MakerWear/MakerWear/Common/Wiki/images/Action/LightBar.png

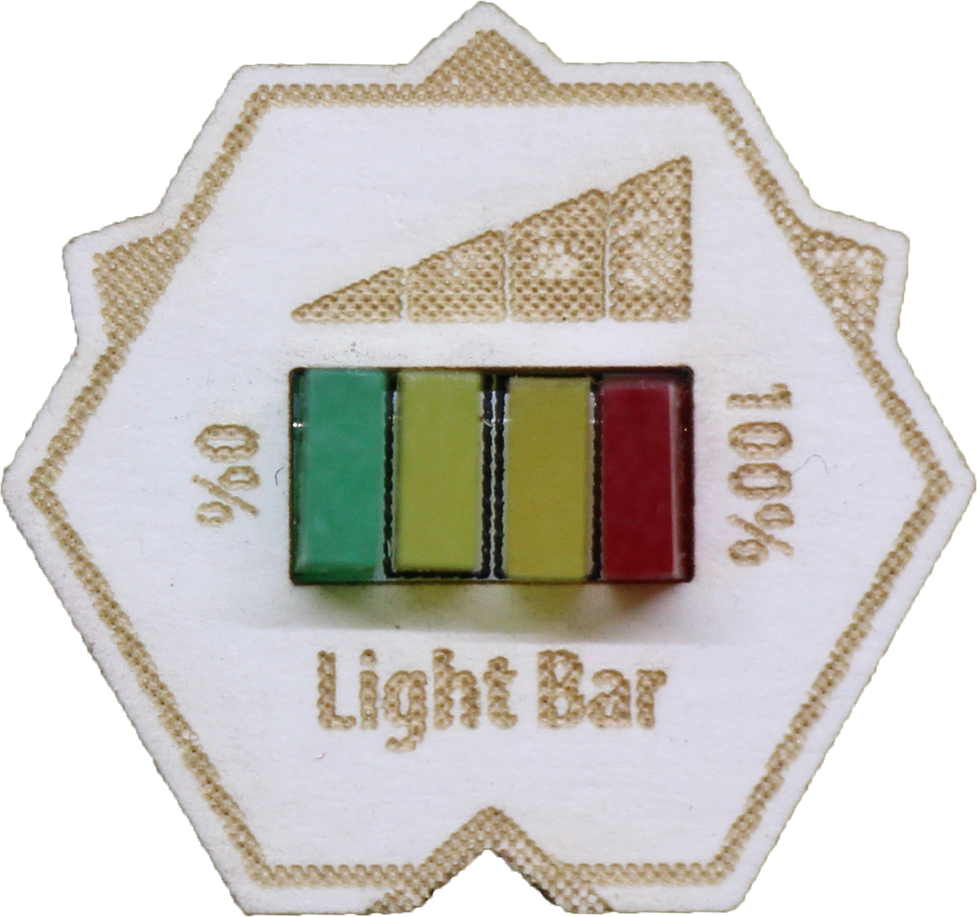
Common/Wiki/images/Action/LightBar.png
