MakerWear/MakerWear/Common/Wiki/images/Action/MultiColorLight.png

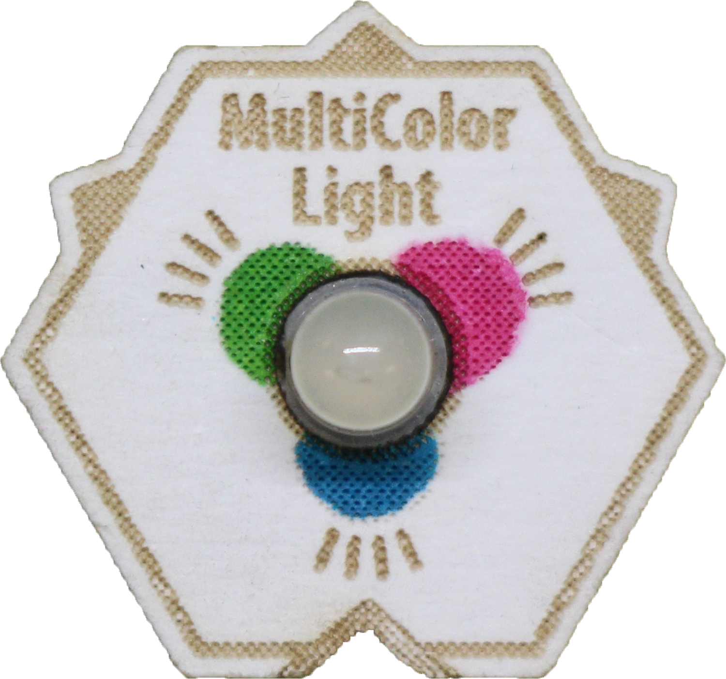
Common/Wiki/images/Action/MultiColorLight.png
