MakerWear/MakerWear/Common/Wiki/images/Action/Number.png

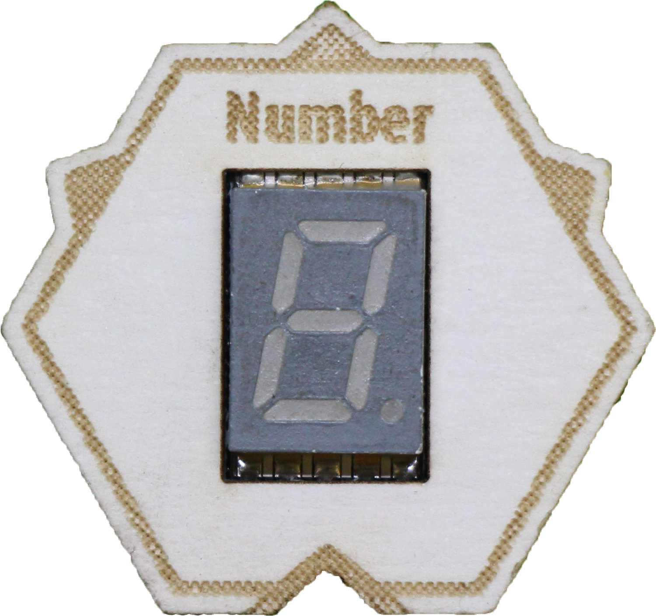
Common/Wiki/images/Action/Number.png
