MakerWear/MakerWear/Common/Wiki/images/Action/RotatorWithPropeller.png

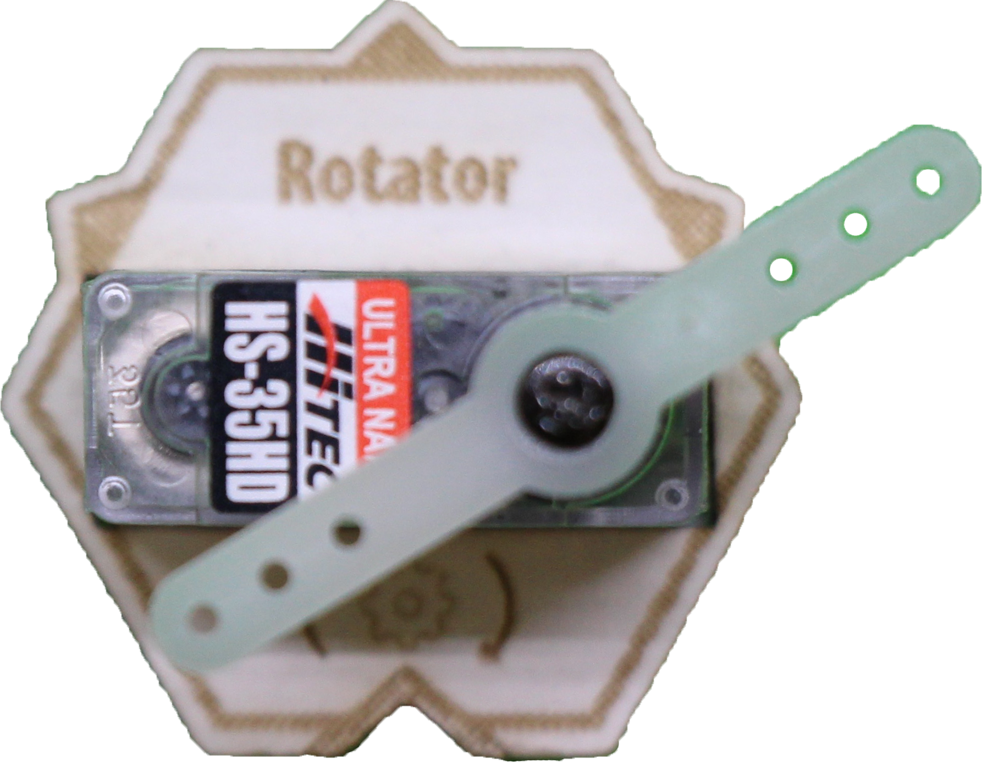
Common/Wiki/images/Action/RotatorWithPropeller.png
