MakerWear/MakerWear/Common/Wiki/images/Action/Sender.png

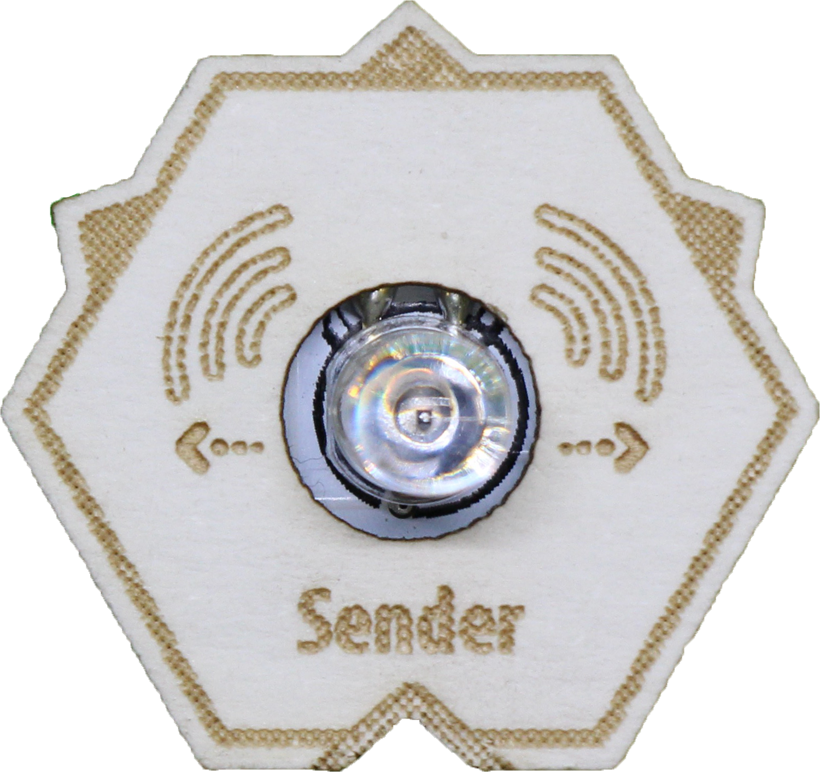
Common/Wiki/images/Action/Sender.png
