MakerWear/MakerWear/Common/Wiki/images/Action/SingleLightRed.png

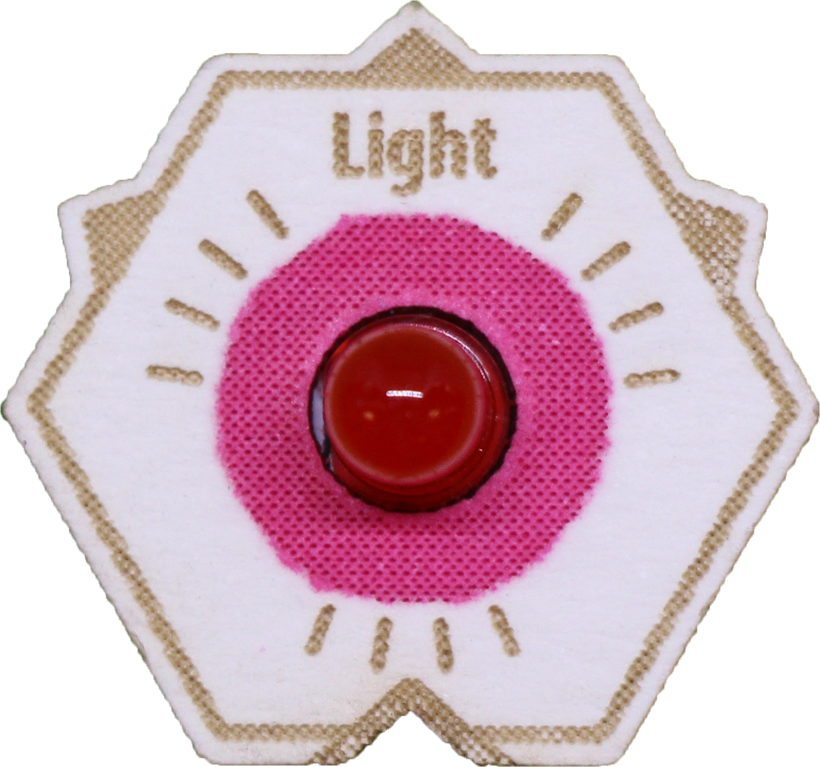
Common/Wiki/images/Action/SingleLightRed.png
