MakerWear/MakerWear/Common/Wiki/images/Action/Spinner_v2.png

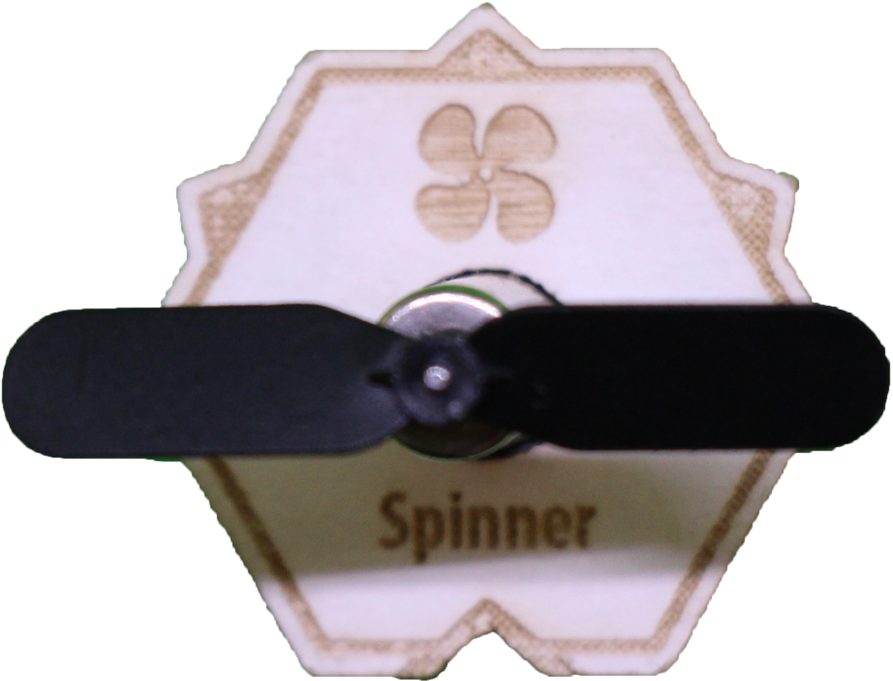
Common/Wiki/images/Action/Spinner_v2.png
