MakerWear/MakerWear/Common/Wiki/images/Action/Vibration.png

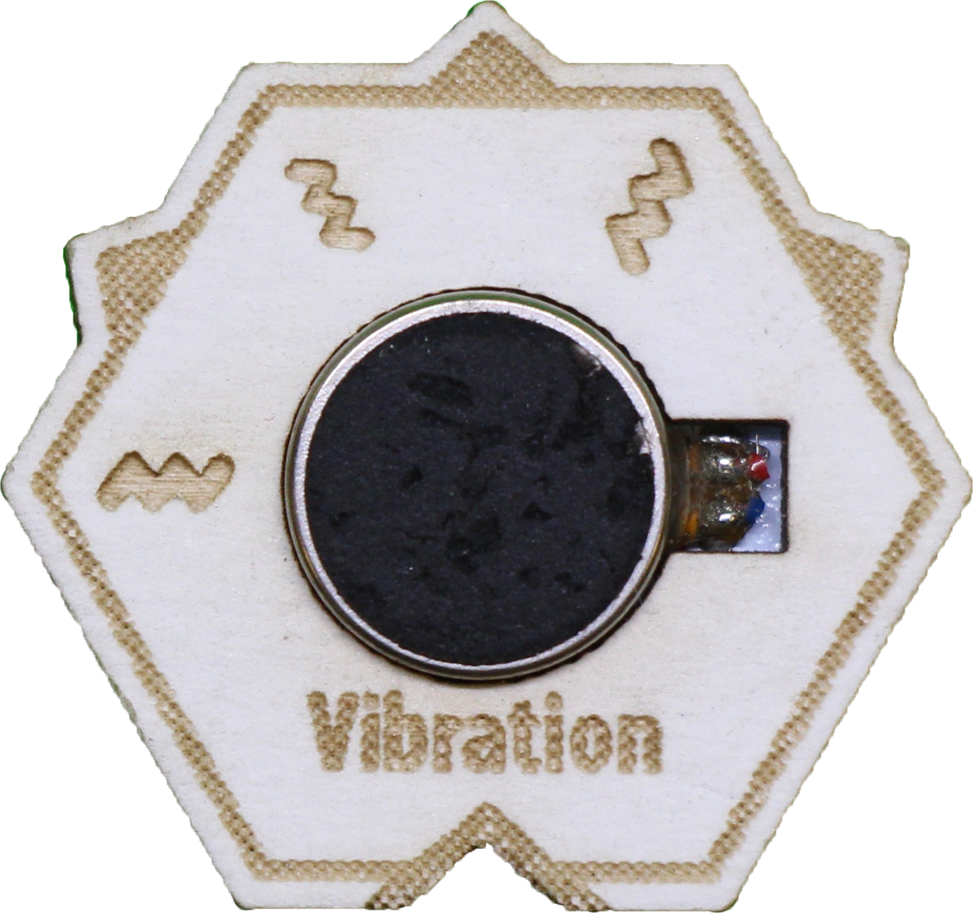
Common/Wiki/images/Action/Vibration.png
