MakerWear/MakerWear/Common/Wiki/images/header.JPG

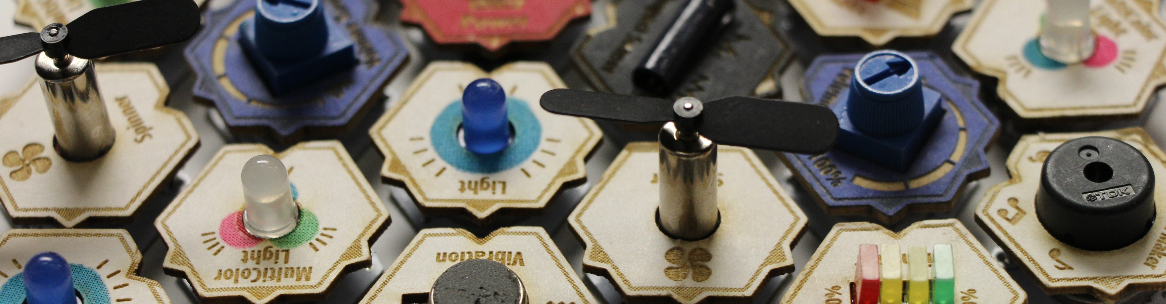
Common/Wiki/images/header.JPG
