MakerWear/MakerWear/Common/Wiki/images/Misc/DIY.png

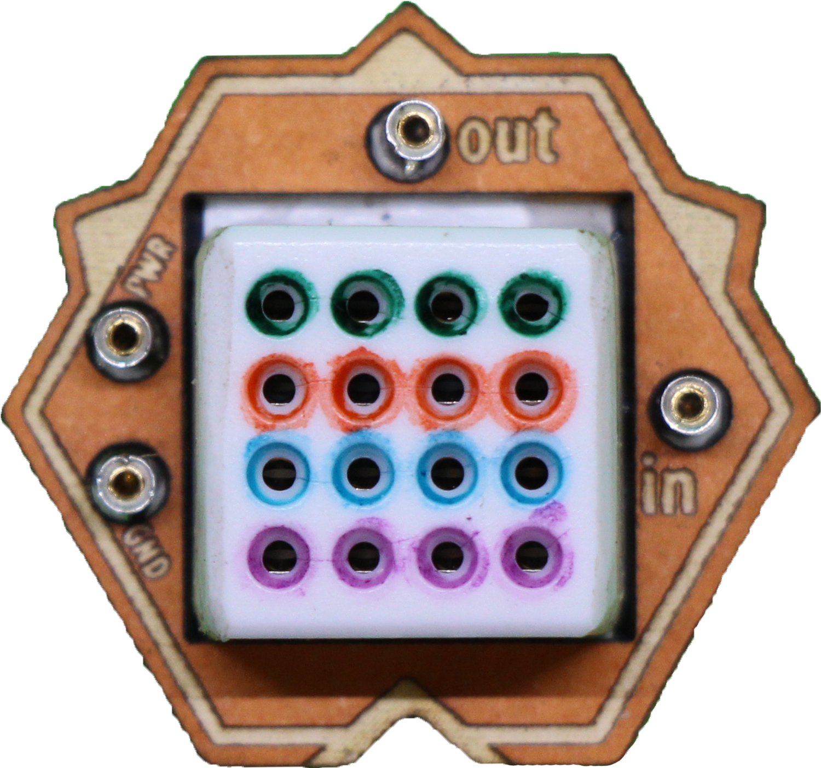
Common/Wiki/images/Misc/DIY.png
