MakerWear/MakerWear/Common/Wiki/images/Misc/Dummy.png

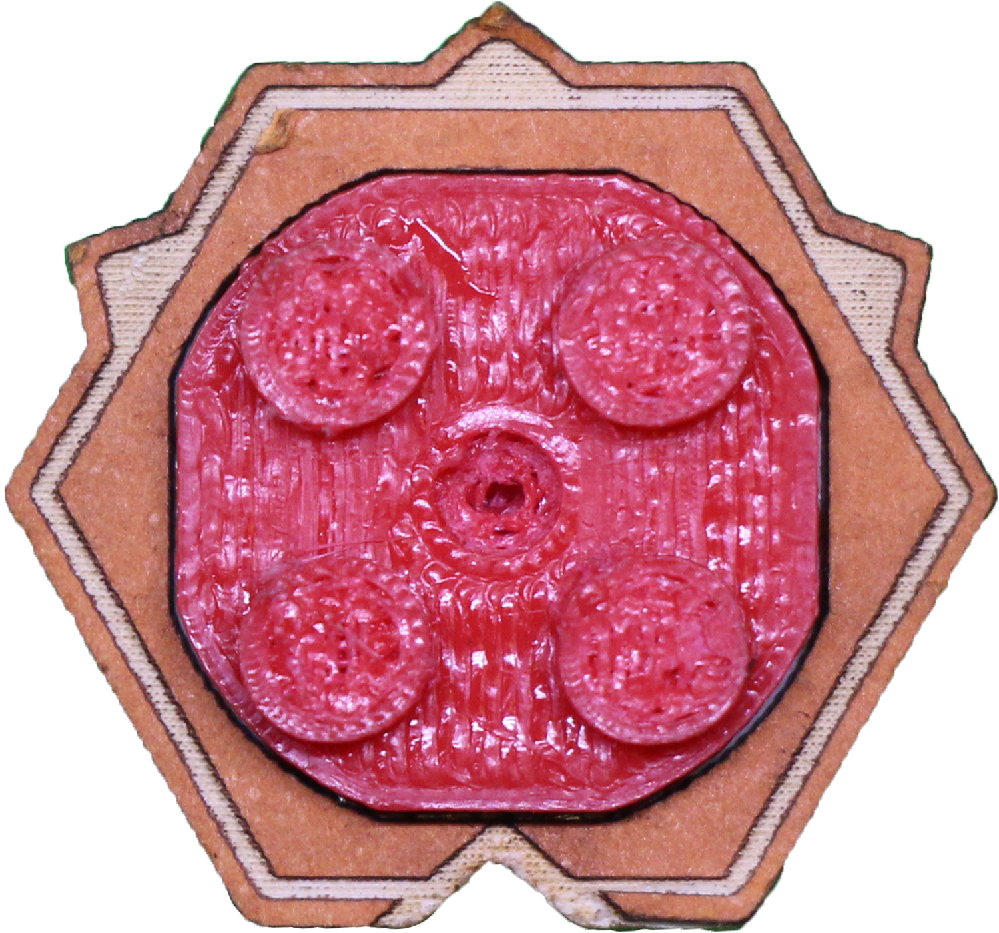
Common/Wiki/images/Misc/Dummy.png
