MakerWear/MakerWear/Common/Wiki/images/Misc/WireEnd.png

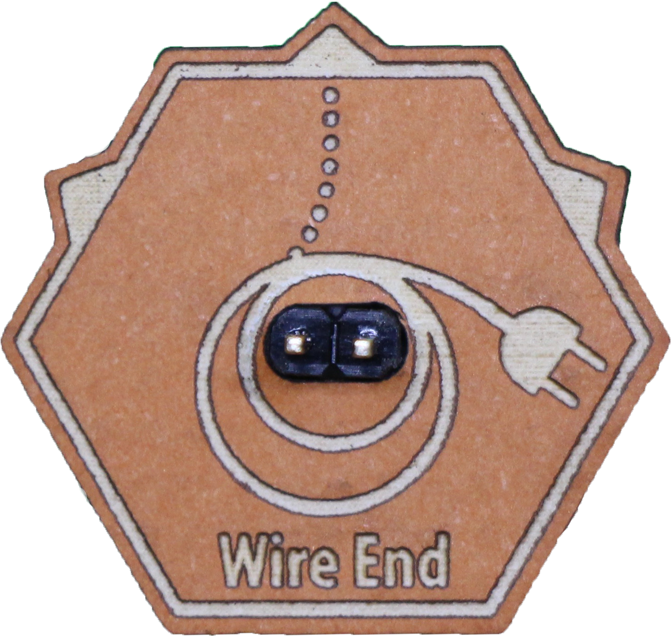
Common/Wiki/images/Misc/WireEnd.png
