MakerWear/MakerWear/Common/Wiki/images/Misc/WireStart.png

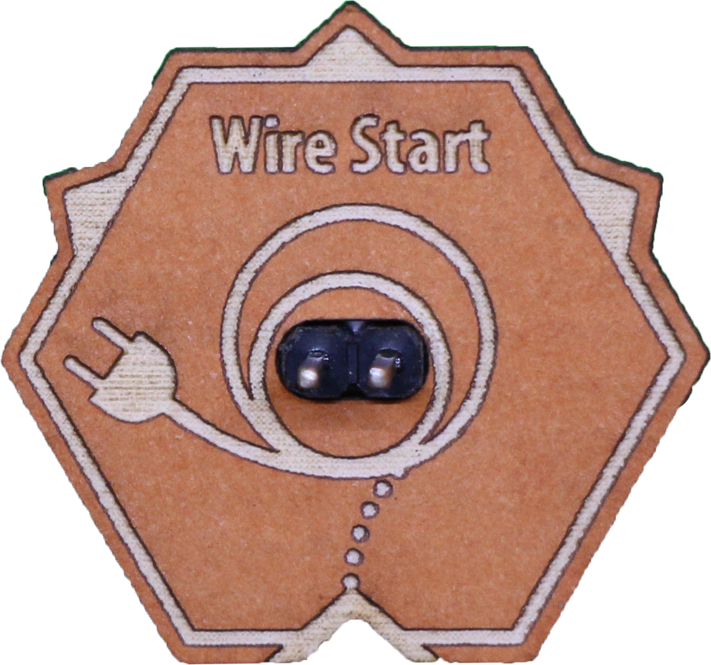
Common/Wiki/images/Misc/WireStart.png
