MakerWear/MakerWear/Common/Wiki/images/Modifier/Counter.png

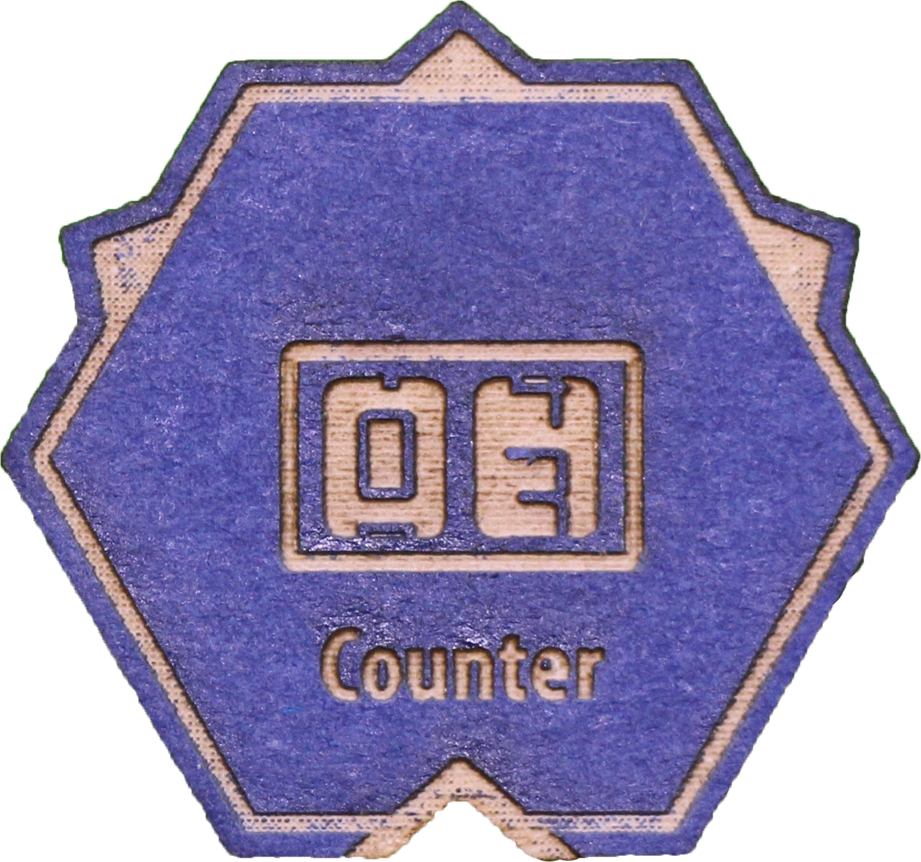
Common/Wiki/images/Modifier/Counter.png
