MakerWear/MakerWear/Common/Wiki/images/Modifier/Fade.png

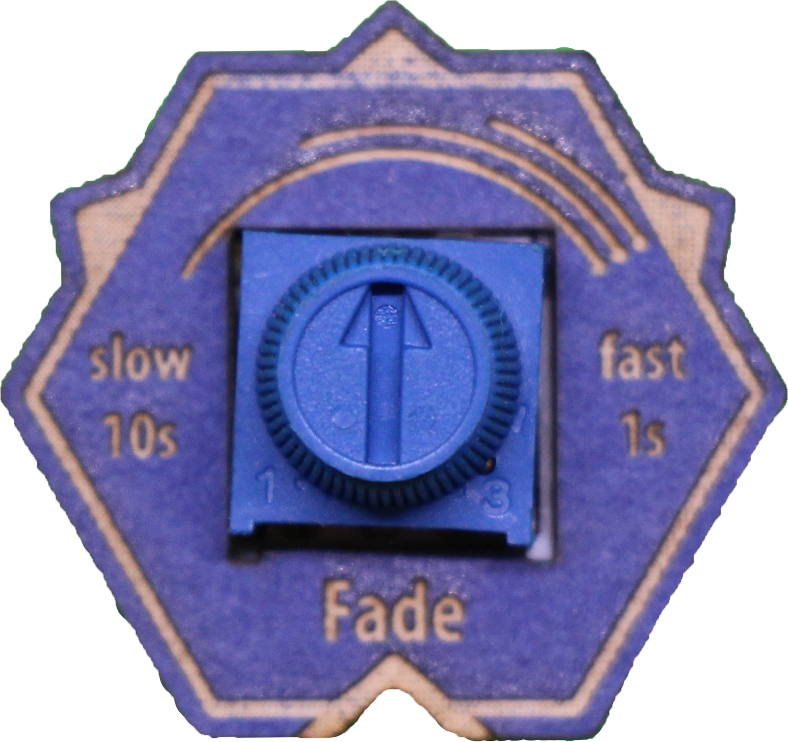
Common/Wiki/images/Modifier/Fade.png
