MakerWear/MakerWear/Common/Wiki/images/Modifier/Inverter.png

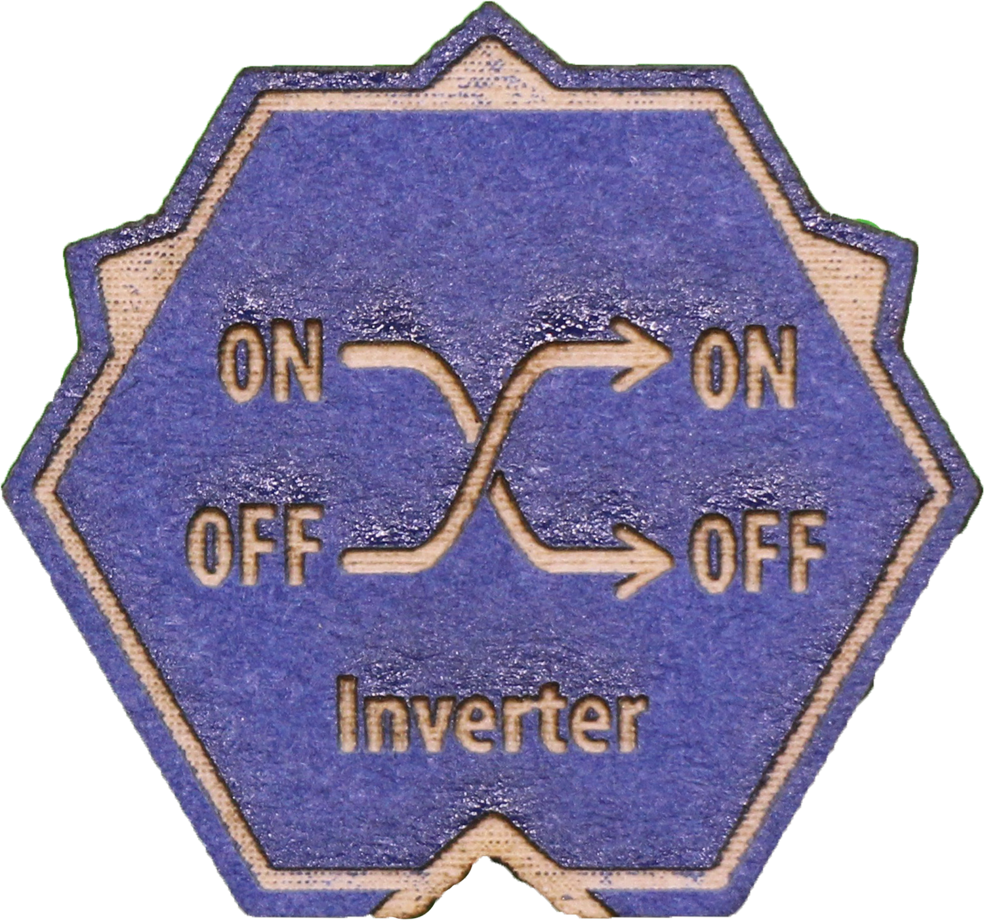
Common/Wiki/images/Modifier/Inverter.png
