MakerWear/MakerWear/Common/Wiki/images/Modifier/SineWave.png

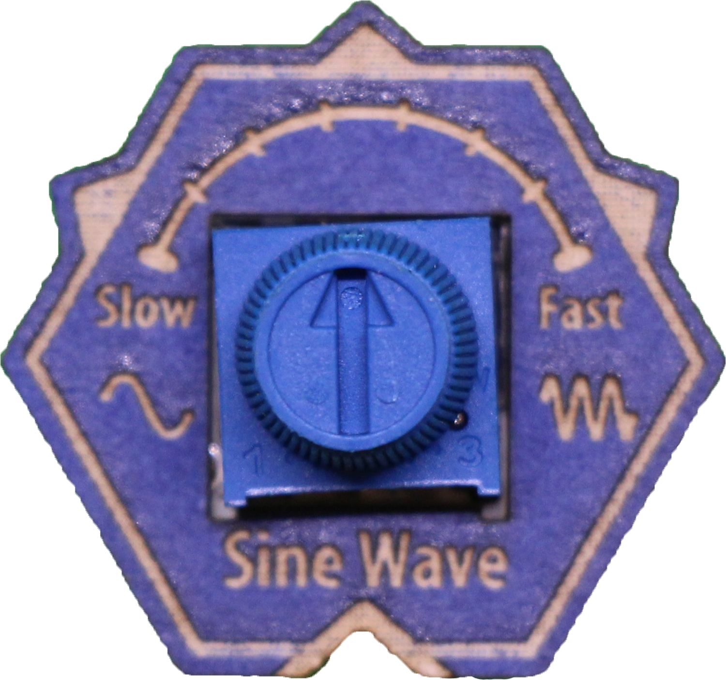
Common/Wiki/images/Modifier/SineWave.png
