MakerWear/MakerWear/Common/Wiki/images/Modifier/SquareWave.png

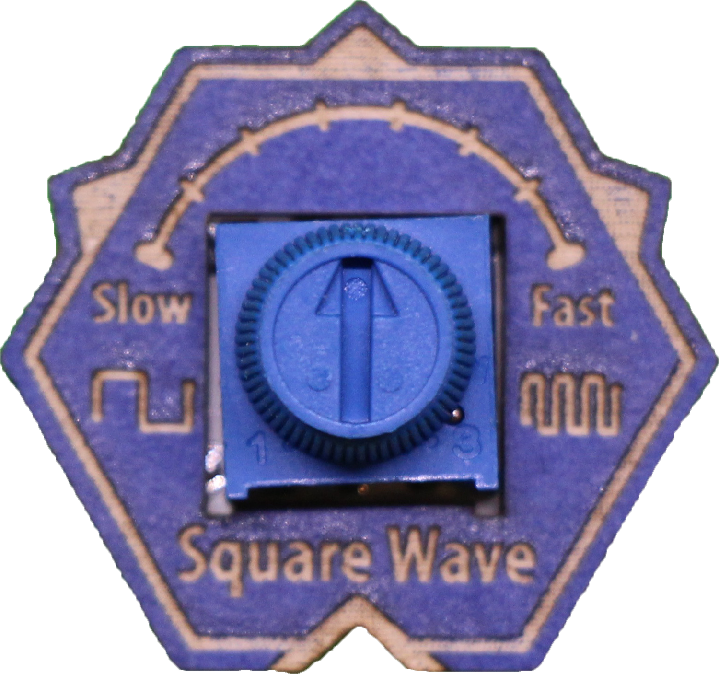
Common/Wiki/images/Modifier/SquareWave.png
