MakerWear/MakerWear/Common/Wiki/images/Modifier/VolumeKnob.png

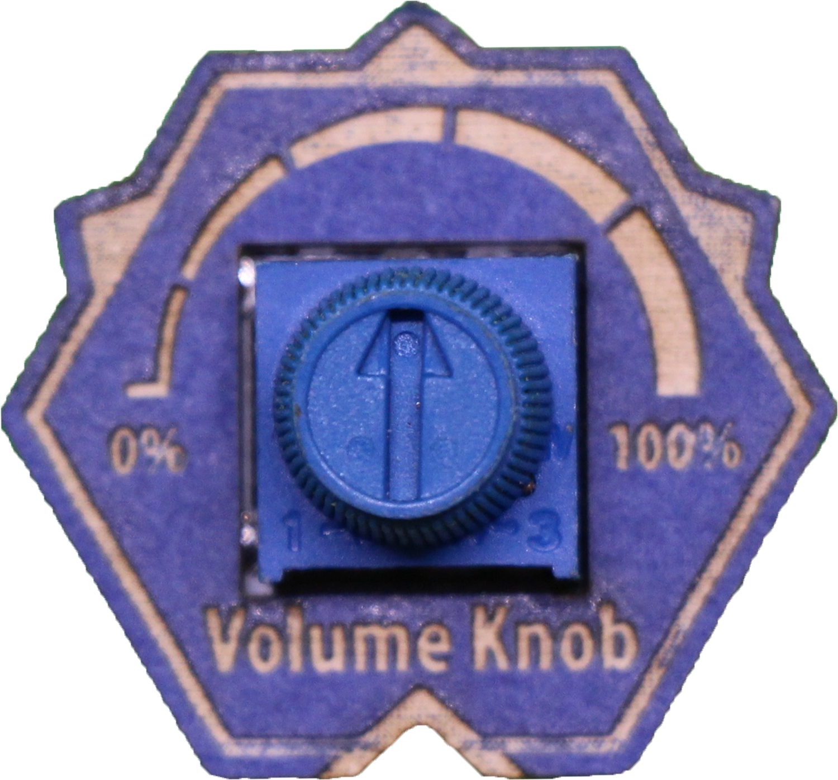
Common/Wiki/images/Modifier/VolumeKnob.png
