MakerWear/MakerWear/Common/Wiki/images/Power/power.png

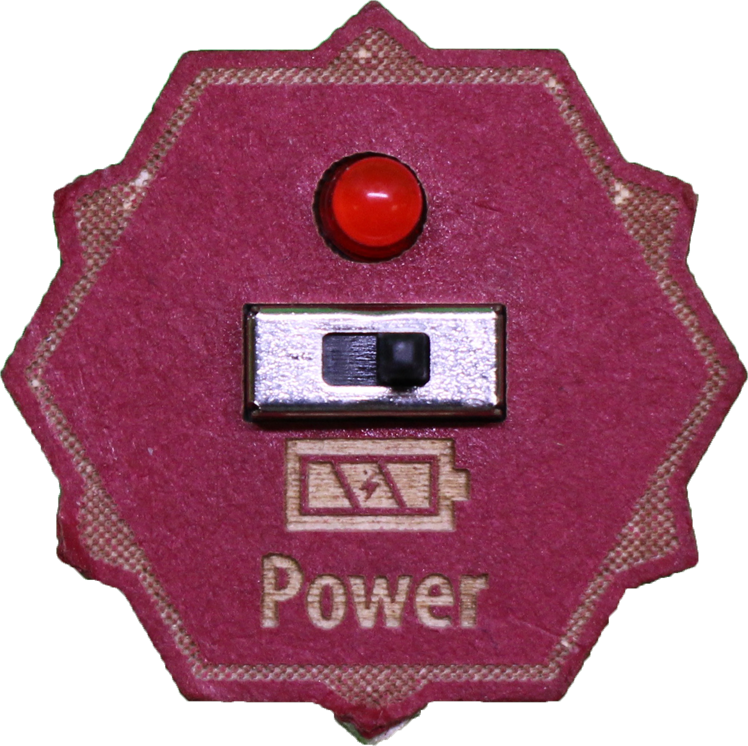
Common/Wiki/images/Power/power.png
