MakerWear/MakerWear/Common/Wiki/images/Sensor/ColorDetector.png

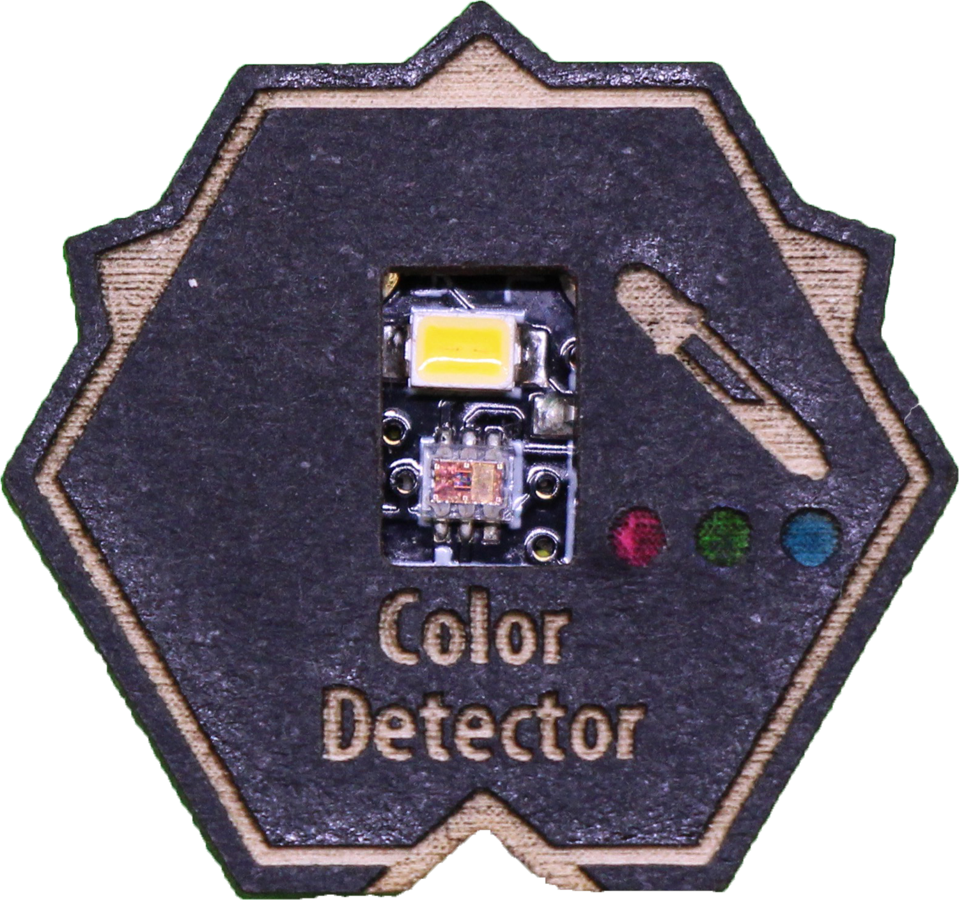
Common/Wiki/images/Sensor/ColorDetector.png
