MakerWear/MakerWear/Common/Wiki/images/Sensor/DistanceSensor.png

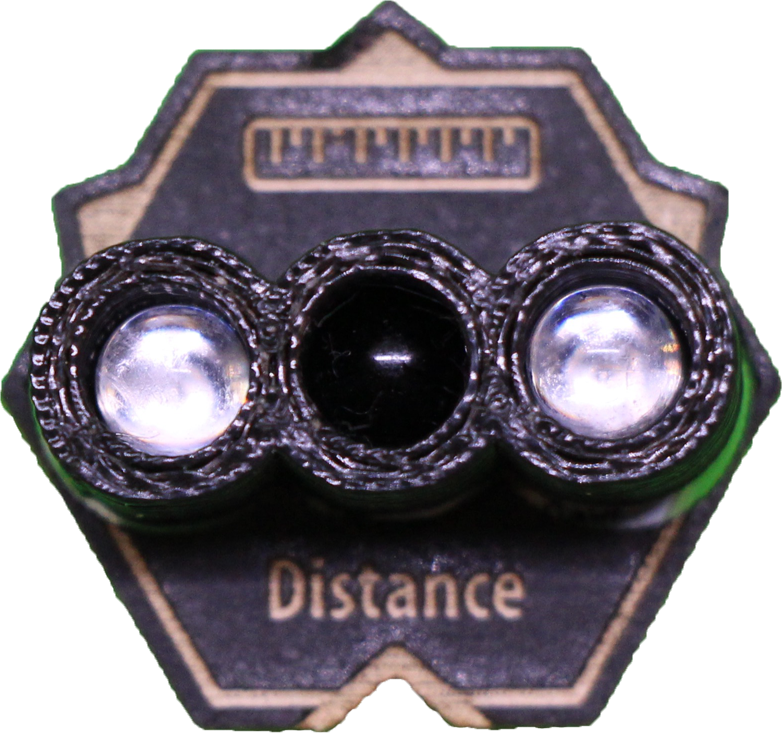
Common/Wiki/images/Sensor/DistanceSensor.png
