MakerWear/MakerWear/Common/Wiki/images/Sensor/ImpactSensor.png

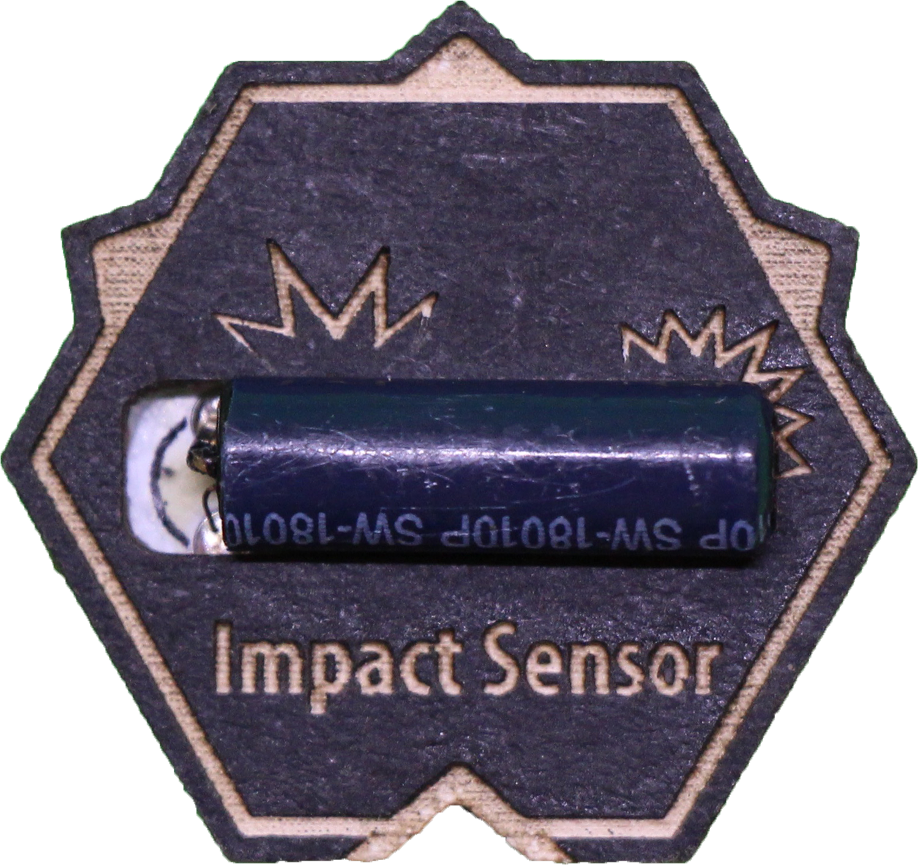
Common/Wiki/images/Sensor/ImpactSensor.png
