MakerWear/MakerWear/Common/Wiki/images/Sensor/MotionDetector.png

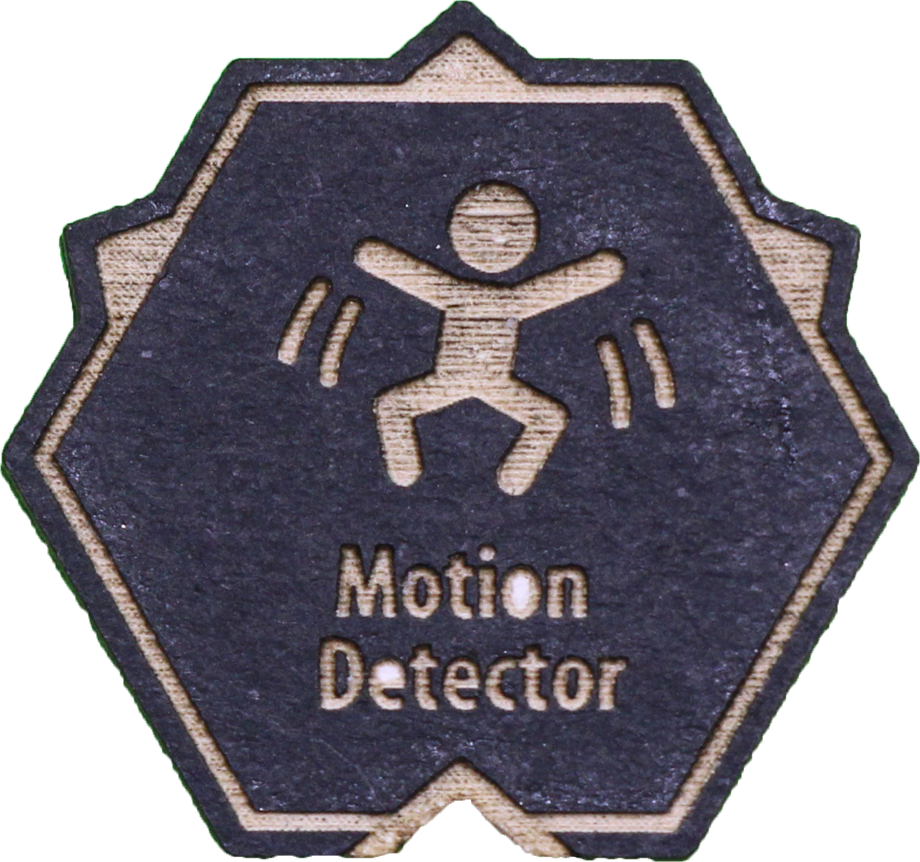
Common/Wiki/images/Sensor/MotionDetector.png
