MakerWear/MakerWear/Common/Wiki/images/Sensor/Receiver.png

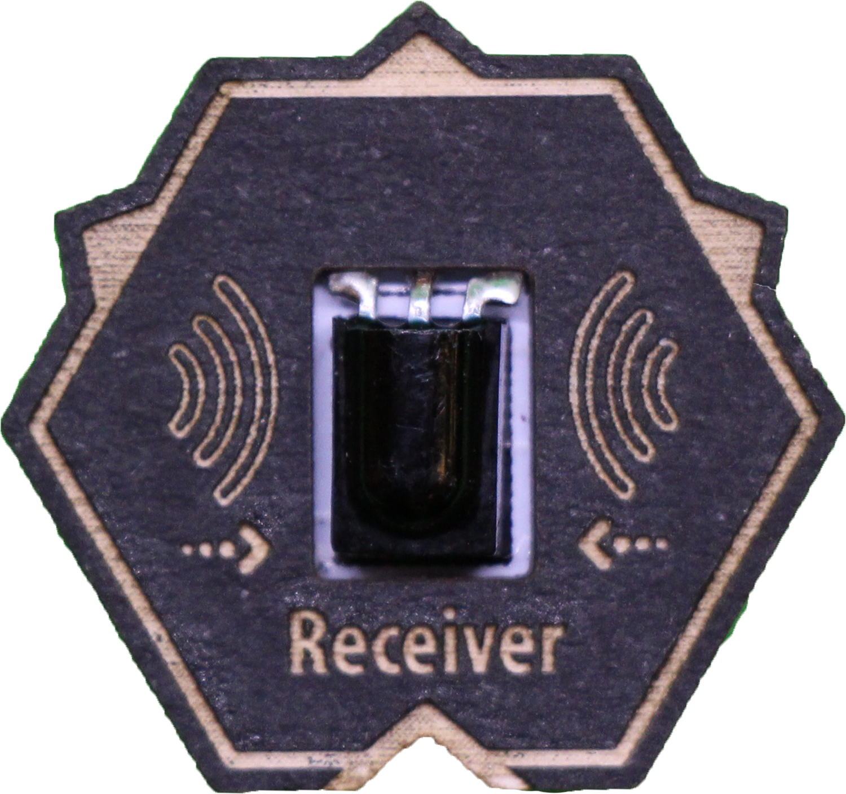
Common/Wiki/images/Sensor/Receiver.png
