MakerWear/MakerWear/Common/Wiki/images/Sensor/TemperatureSensor.png

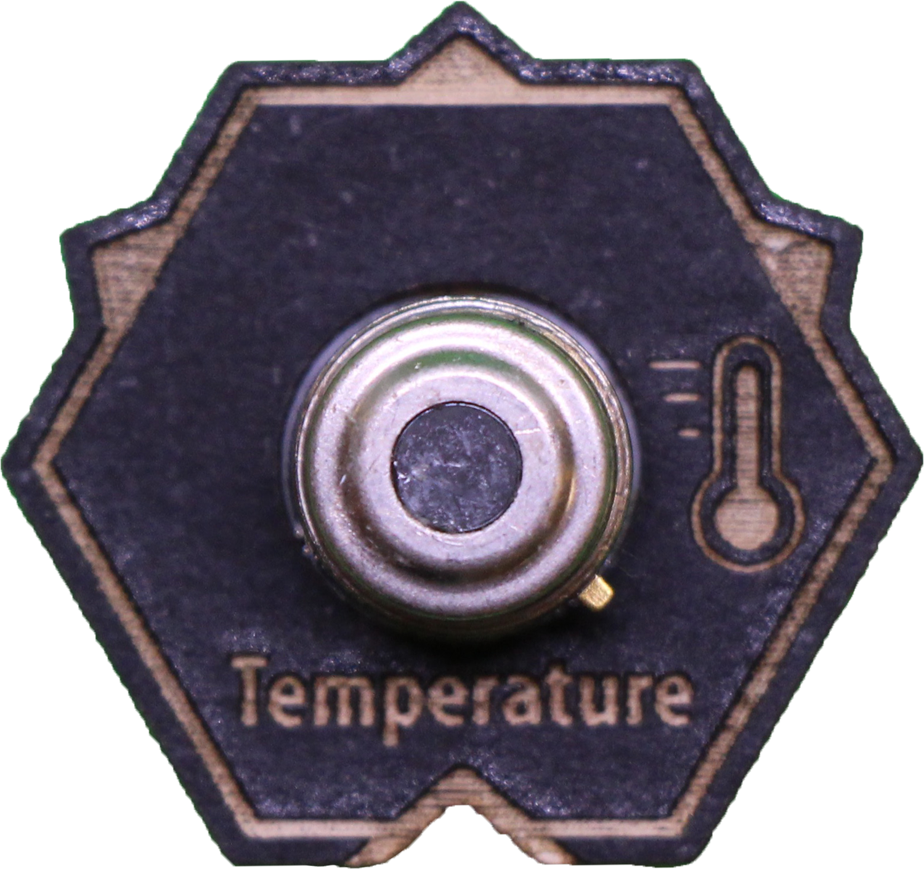
Common/Wiki/images/Sensor/TemperatureSensor.png
