MakerWear/MakerWear/Common/Wiki/images/Sensor/TiltSensor.png

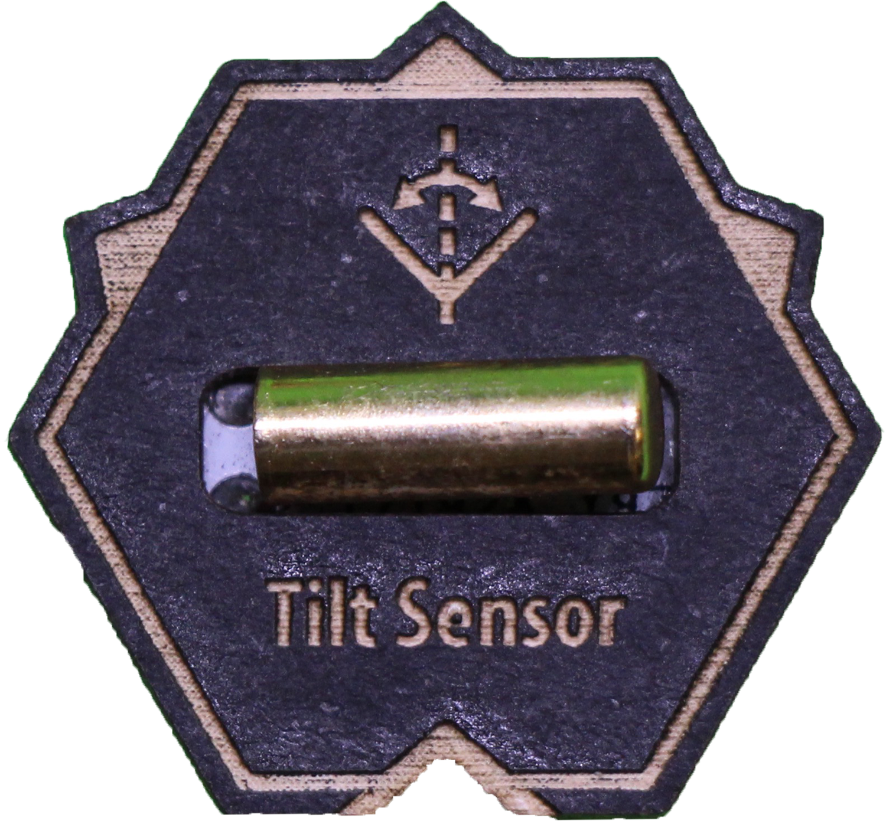
Common/Wiki/images/Sensor/TiltSensor.png
