MakerWear/MakerWear/Modules/Sensor/DistanceSensor/ArduinoCodes/2LEDcurve.jpg

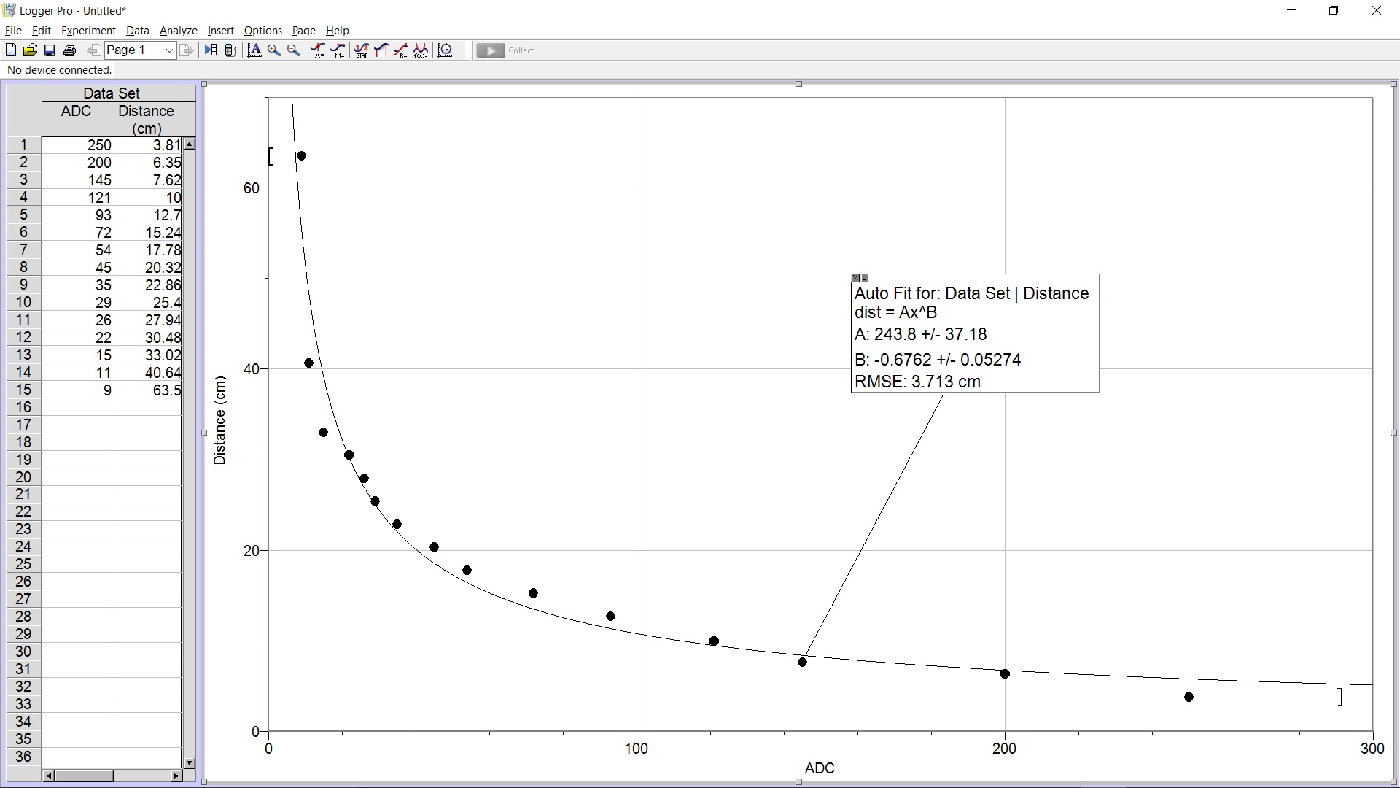
Modules/Sensor/DistanceSensor/ArduinoCodes/2LEDcurve.jpg
