MakerWear/MakerWear/Modules/Misc/ProgrammableOLED/EagleDesigns/ComponentList.xlsx

Name | Link | Dimensions | Count | Price | Notes
Micro OLED | https://www.sparkfun.com/products/13003 |  | 1 |  | For making this module, we desoldered the OLED from the Sparkfun breakout board using a soldering Iron and soldered it on top of our own custom PCB
ATmega328P-AU-ND | http://www.digikey.com/short/3pr0nz | 32TQFP | 1
Shield Finger Contact Spring | http://www.digikey.com/short/3zzmh1 | SMD | 9
1MΩ SMD Resistor | http://www.digikey.com/short/35mdtn | 0603 | 3
4x2 Pin Header | http://www.digikey.com/short/35md8j | 2.54mm Pitch | 1
4.7KΩ Resistor | http://www.digikey.com/short/35mdfh | 0603 | 3
0.22uF Capacitor | http://www.digikey.com/short/35rjqv | 0603 | 3
Micro USB Connector | http://www.digikey.com/short/35mvjp | SMD | 1
390KΩ Resistor | http://www.digikey.com/short/35rqbz | 0603
1uF Capacitor | http://www.digikey.com/short/35rq5v | 0603 | 2
