MakerWear/MakerWear/Modules/Sensor/DistanceSensor/EagleDesigns/ComponentList.xlsx

Name | Link | Dimensions | Count | Price | Notes
4.7KΩ Resistor | http://www.digikey.com/short/35mdfh | 0603 | 1
0.22uF Capacitor | http://www.digikey.com/short/35rjqv | 0603 | 1
ATtiny85-20PU | http://www.digikey.com/short/3zphbw | DIP | 1
Shield Finger Contact Spring | http://www.digikey.com/short/3zzmh1 | SMD | 6
1MΩ SMD Resistor | http://www.digikey.com/short/35mdtn | 0603 | 1
4x1 Pin Header | http://www.digikey.com/short/3zzh43 | 2.54mm Pitch | 1
Infrared Receiver | http://a.co/4VBF2Ul | Through Hole | 1
Infrared Emitter | http://a.co/4VBF2Ul | Through Hole | 2
100KΩ Resistor | https://www.digikey.com/short/3n01hw | 0603 | 1
3D Printed Casing |  |  | 1
