MakerWear/MakerWear/Modules/Sensor/LightSensor/EagleDesigns/ComponentList.xlsx

Name | Link | Dimensions | Count | Price | Notes
4.7KΩ Resistor | http://www.digikey.com/short/35mdfh | 0603 | 2
0.22uF Capacitor | http://www.digikey.com/short/35rjqv | 0603 | 1
ATtiny85-20PU | http://www.digikey.com/short/3zphbw | DIP | 1
Shield Finger Contact Spring | http://www.digikey.com/short/3zzmh1 | SMD | 6
1MΩ SMD Resistor | http://www.digikey.com/short/35mdtn | 0603 | 1
4x1 Pin Header | http://www.digikey.com/short/3zzh43 | 2.54mm Pitch | 1
330KΩ Resistor | https://www.digikey.com/short/3nvcp9 | 0603 | 1
Photoresistor | https://www.sparkfun.com/products/9088 | Through Hole | 1 |  | I was not able to find the photoresistor that we used in our current modules (we used the ones that we had in our lab) and thus the code or the pull-up resistor might need to be re-calibrated.
