MakerWear/MakerWear/Modules/Sensor/Receiver/EagleDesigns/ComponentList.xlsx

Name | Link | Dimensions | Count | Price | Notes
4.7KΩ Resistor | http://www.digikey.com/short/35mdfh | 0603 | 1
0.22uF Capacitor | http://www.digikey.com/short/35rjqv | 0603 | 1
ATmega328P-AU-ND | http://www.digikey.com/short/3pr0nz | 32TQFP | 1
Shield Finger Contact Spring | http://www.digikey.com/short/3zzmh1 | SMD | 6
1MΩ SMD Resistor | http://www.digikey.com/short/35mdtn | 0603 | 1
4x1 Pin Header | http://www.digikey.com/short/3zzh43 | 2.54mm Pitch | 1
38KHz IR Receiver | http://www.digikey.com/short/3zpt9f | Through Hole | 1 |  | It is through hole, but we solder it like a SMD component using a soldering iron (not in the oven)
