MakerWear/MakerWear/Common/BasePCBs/3x3/bottom/Dimensions/dxf/3x3Bottom_contacts.dxf

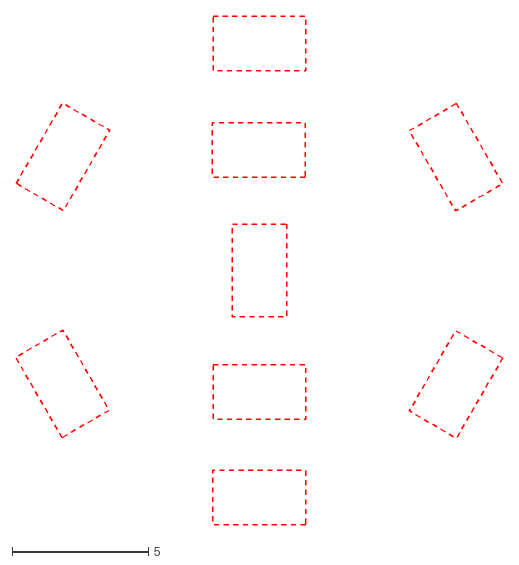
[picture p49: CAD file, 2016-11-28]
Common/BasePCBs/3x3/bottom/Dimensions/dxf/3x3Bottom_contacts.dxf
17.9 x 18.7
