MakerWear/MakerWear/Common/BasePCBs/3x3/top/Dimensions/dxf/3x3Top_outline(a).dxf

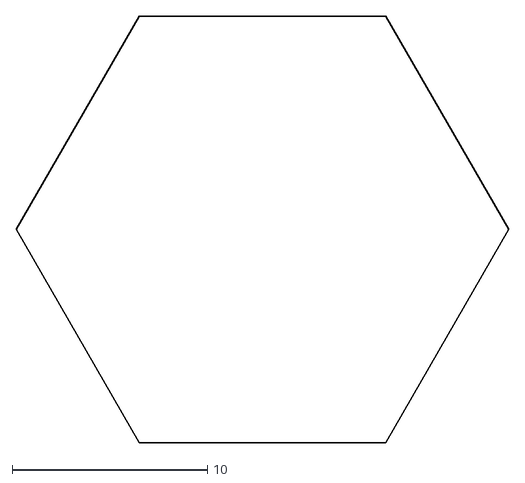
[picture p50: CAD file, 2016-11-15]
Common/BasePCBs/3x3/top/Dimensions/dxf/3x3Top_outline(a).dxf
25.2 x 21.8
