MakerWear/MakerWear/Common/BasePCBs/3x3Bottom/Dimensions/outline_b.dxf

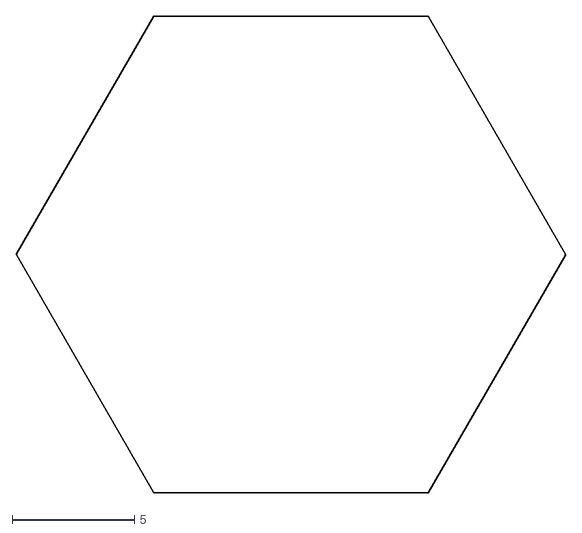
[picture p51: CAD file, 2016-09-28]
Common/BasePCBs/3x3Bottom/Dimensions/outline_b.dxf
22.5 x 19.5
