MakerWear/MakerWear/Common/BasePCBs/Socket/Dimensions/dxf/socket_board_outline(a).dxf

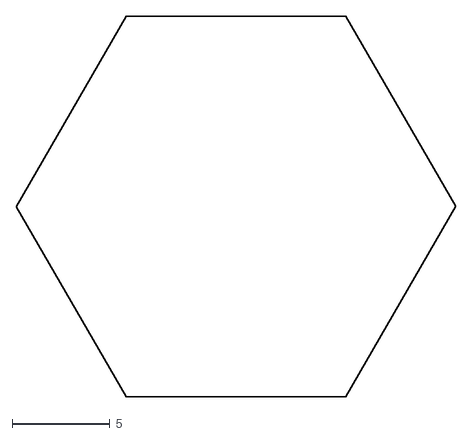
[picture p52: CAD file, 2016-06-12]
Common/BasePCBs/Socket/Dimensions/dxf/socket_board_outline(a).dxf
22.5 x 19.5
