MakerWear/MakerWear/Common/BasePCBs/0x6/Bottom/Dimensions/dxf/0x6_bottom_bLayer.dxf

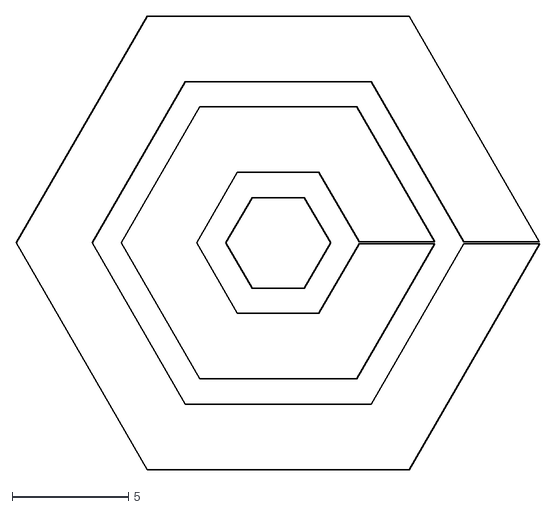
[picture p53: CAD file, 2016-06-12]
Common/BasePCBs/0x6/Bottom/Dimensions/dxf/0x6_bottom_bLayer.dxf
22.5 x 19.5
