MakerWear/MakerWear/Common/BasePCBs/0x6/Top/Dimensions/dxf/0x6_top_board_outline(a).dxf

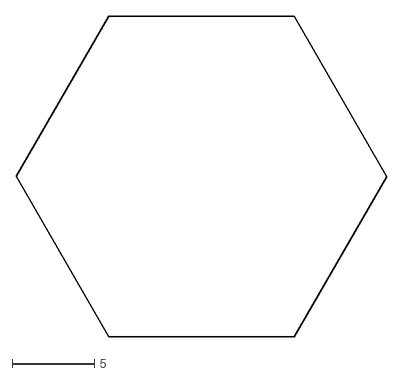
[picture p54: CAD file, 2016-06-12]
Common/BasePCBs/0x6/Top/Dimensions/dxf/0x6_top_board_outline(a).dxf
22.5 x 19.5
