MakerWear/MakerWear/Common/BasePCBs/1x3/Bottom/Dimensions/dxf/1x3_bottom_bLayer (c).dxf

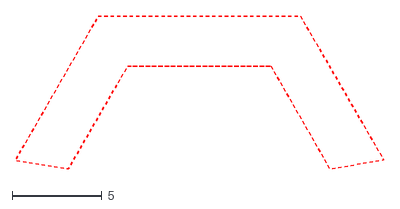
[picture p55: CAD file, 2016-06-12]
Common/BasePCBs/1x3/Bottom/Dimensions/dxf/1x3_bottom_bLayer (c).dxf
20.5 x 8.52
