MakerWear/MakerWear/Common/BasePCBs/1x3/TopLarge/Dimensions/1x3Top_outline(b).dxf

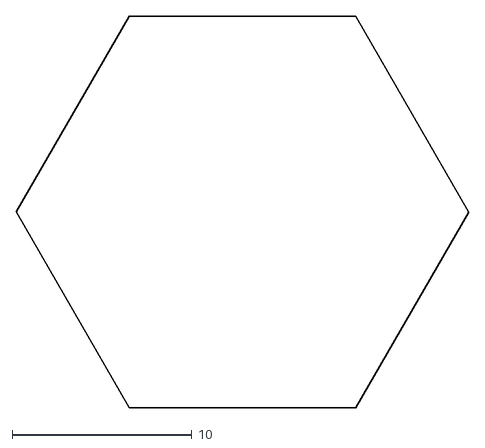
[picture p56: CAD file, 2016-12-02]
Common/BasePCBs/1x3/TopLarge/Dimensions/1x3Top_outline(b).dxf
25.2 x 21.8
