MakerWear/MakerWear/Common/BasePCBs/3x3/bottom/Dimensions/dxf/3x3Bottom_outline(b).dxf

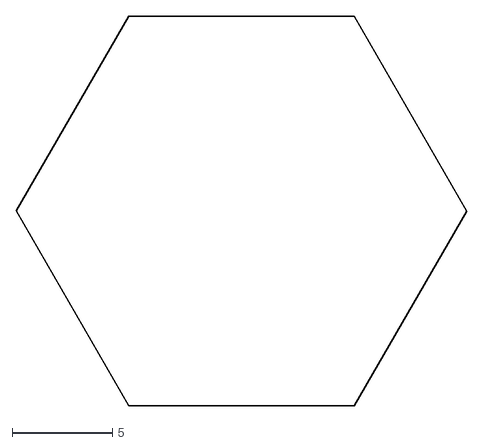
[picture p57: CAD file, 2016-11-28]
Common/BasePCBs/3x3/bottom/Dimensions/dxf/3x3Bottom_outline(b).dxf
22.5 x 19.5
