MakerWear/MakerWear/Common/BasePCBs/3x3/top/Dimensions/dxf/3x3Top_pins.dxf

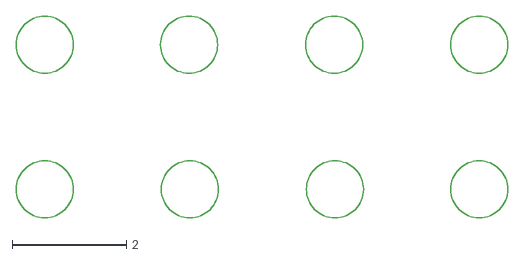
[picture p58: CAD file, 2016-11-15]
Common/BasePCBs/3x3/top/Dimensions/dxf/3x3Top_pins.dxf
8.61 x 3.53
