MakerWear/MakerWear/Common/BasePCBs/Socket/Dimensions/dxf/socket_tPlace.dxf

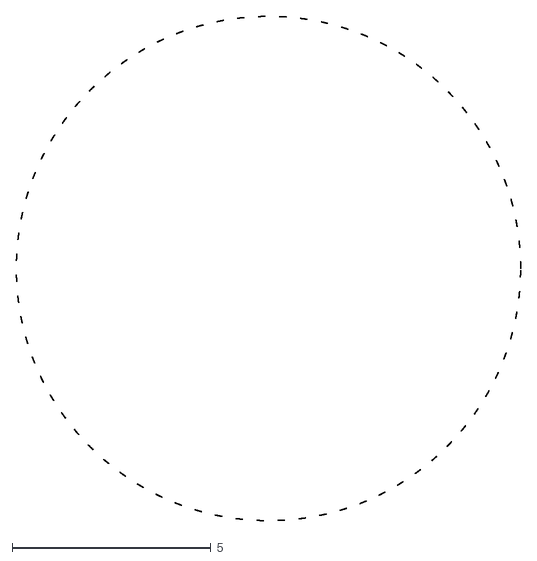
[picture p60: CAD file, 2016-06-12]
Common/BasePCBs/Socket/Dimensions/dxf/socket_tPlace.dxf
12.7 x 12.7
