MakerWear/MakerWear/Common/BasePCBs/0x6/Bottom/Dimensions/dxf/0x6_bottom_bDoc.dxf

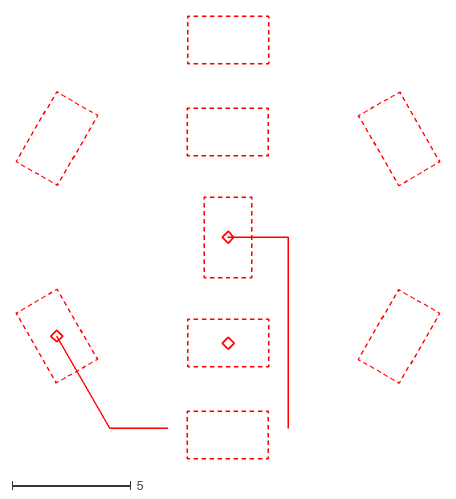
[picture p61: CAD file, 2016-06-12]
Common/BasePCBs/0x6/Bottom/Dimensions/dxf/0x6_bottom_bDoc.dxf
17.9 x 18.7
