MakerWear/MakerWear/Common/BasePCBs/1x3/Bottom/Dimensions/dxf/1x3_bottom_tPlace.dxf

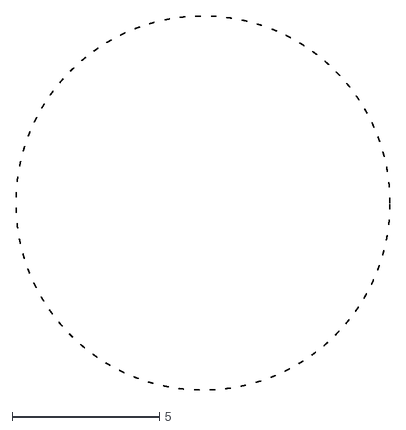
[picture p62: CAD file, 2016-06-12]
Common/BasePCBs/1x3/Bottom/Dimensions/dxf/1x3_bottom_tPlace.dxf
12.7 x 12.7
