MakerWear/MakerWear/Common/BasePCBs/3x3/bottom/Dimensions/dxf/3x3Bottom_outline(a).dxf

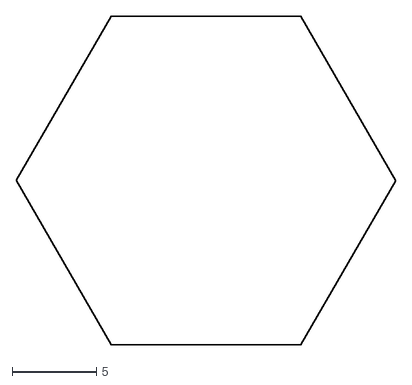
[picture p63: CAD file, 2016-11-28]
Common/BasePCBs/3x3/bottom/Dimensions/dxf/3x3Bottom_outline(a).dxf
22.5 x 19.5
