MakerWear/MakerWear/Common/BasePCBs/Socket/Dimensions/dxf/socket_board_outline(b).dxf

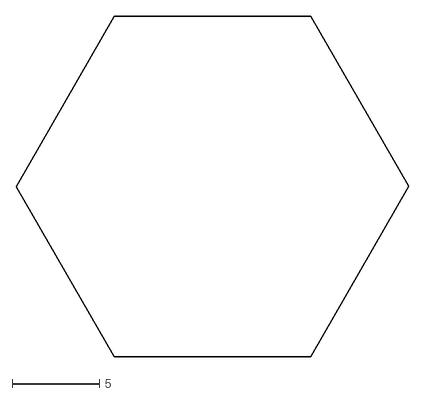
[picture p64: CAD file, 2016-06-12]
Common/BasePCBs/Socket/Dimensions/dxf/socket_board_outline(b).dxf
22.5 x 19.5
