MakerWear/MakerWear/Common/BasePCBs/Socket/Dimensions/dxf/socket_via.dxf

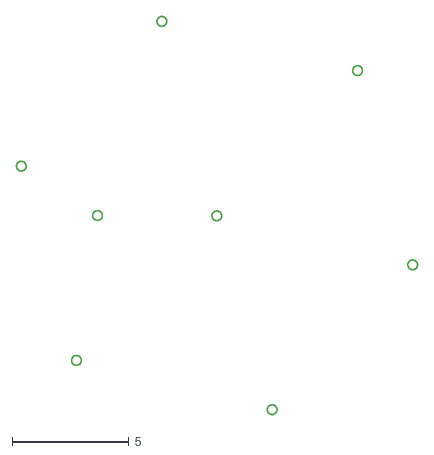
[picture p67: CAD file, 2016-06-12]
Common/BasePCBs/Socket/Dimensions/dxf/socket_via.dxf
17.2 x 17.1
