MakerWear/MakerWear/Common/BasePCBs/0x6/Bottom/Dimensions/dxf/0x6_bottom_tPlace.dxf

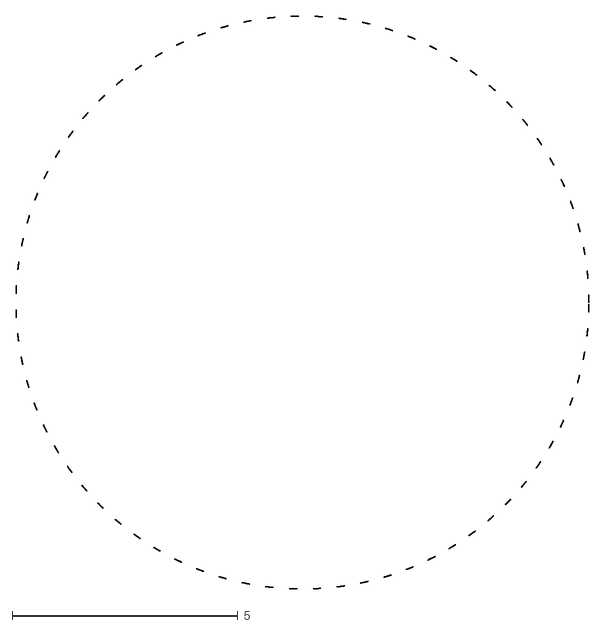
[picture p68: CAD file, 2016-06-12]
Common/BasePCBs/0x6/Bottom/Dimensions/dxf/0x6_bottom_tPlace.dxf
12.7 x 12.7
