MakerWear/MakerWear/Common/BasePCBs/1x3/Bottom/Dimensions/dxf/1x3_bottom_bLayer (b).dxf

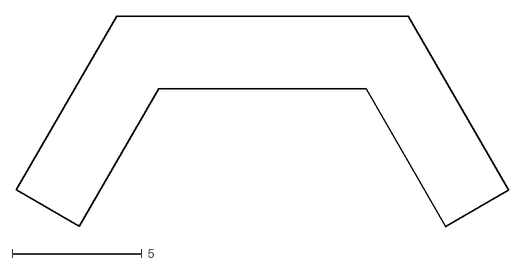
[picture p69: CAD file, 2016-06-12]
Common/BasePCBs/1x3/Bottom/Dimensions/dxf/1x3_bottom_bLayer (b).dxf
19.0 x 8.13
