MakerWear/MakerWear/Common/BasePCBs/Socket/Dimensions/dxf/socket_tLayer.dxf

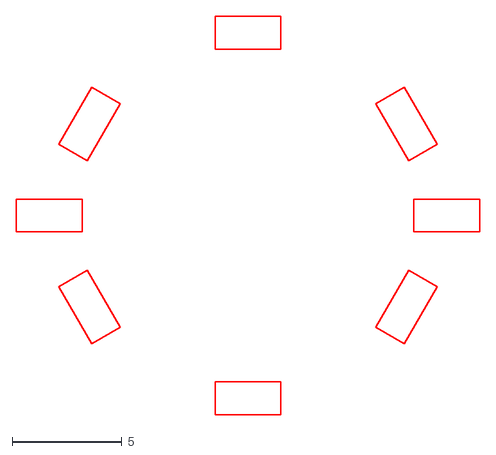
[picture p70: CAD file, 2016-06-12]
Common/BasePCBs/Socket/Dimensions/dxf/socket_tLayer.dxf
21.1 x 18.2
