MakerWear/MakerWear/Common/BasePCBs/1x3/Bottom/Dimensions/dxf/1x3_bottom_bDoc.dxf

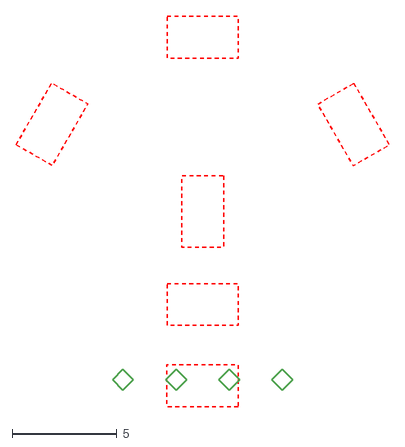
[picture p71: CAD file, 2016-06-12]
Common/BasePCBs/1x3/Bottom/Dimensions/dxf/1x3_bottom_bDoc.dxf
17.8 x 18.7
