MakerWear/MakerWear/Common/BasePCBs/1x3/Bottom/Dimensions/dxf/1x3_bottom_bLayer.dxf

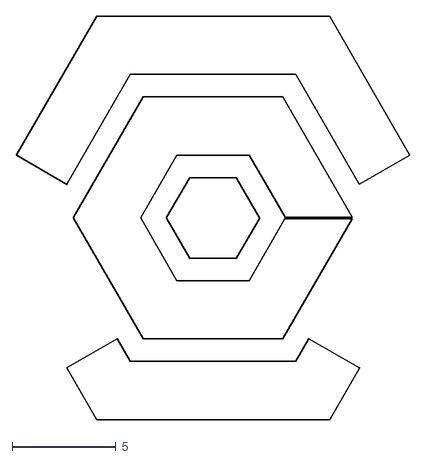
[picture p72: CAD file, 2016-06-12]
Common/BasePCBs/1x3/Bottom/Dimensions/dxf/1x3_bottom_bLayer.dxf
19.0 x 19.5
