MakerWear/MakerWear/Modules/Misc/Dummy/EagleDesigns/Dummy.brd

## EAGLE design Modules/Misc/Dummy/EagleDesigns/Dummy.brd (2016-07-10)

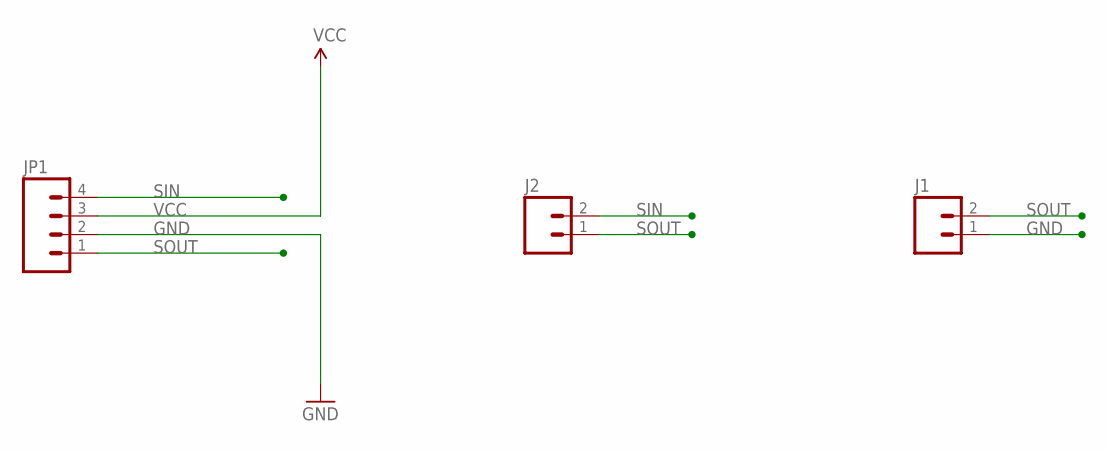
[picture p87: schematic Dummy.sch]

Parts:
J1, J2: M02PTH; 1X02
JP1: M04PTH; 1X04

Connections:
GND: J1.1, JP1.2
SIN: J2.2, JP1.4
SOUT: J1.2, J2.1, JP1.1
VCC: JP1.3
