MakerWear/MakerWear/Modules/Misc/Dummy/EagleDesigns/Dummy.brd

## EAGLE design Modules/Misc/Dummy/EagleDesigns/Dummy.brd (continued)

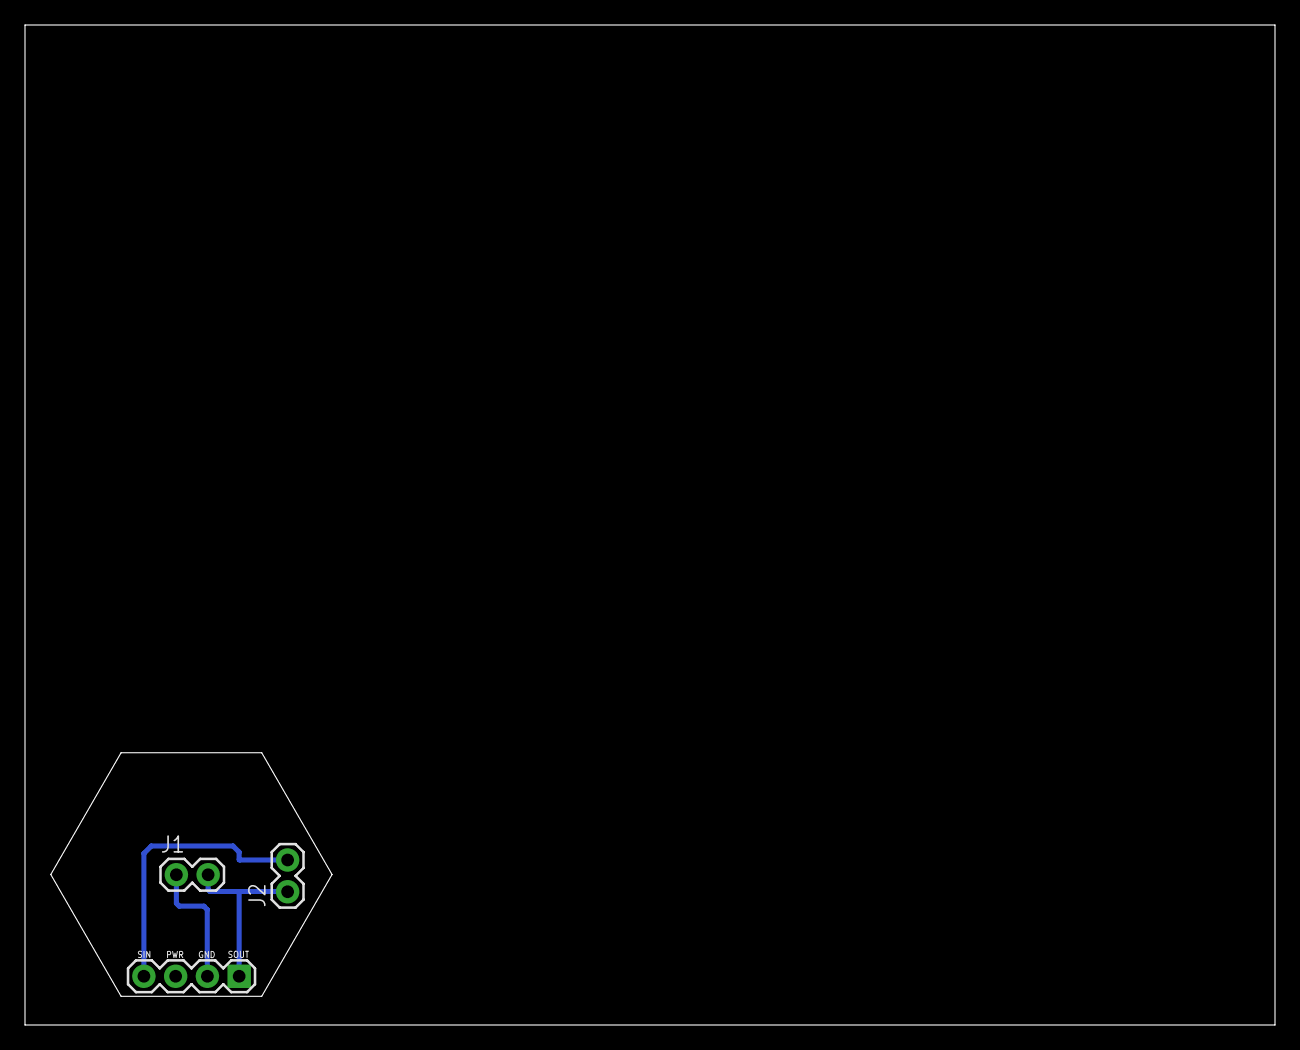
[picture p88: board Dummy.brd from above]

Board: 2 copper layers, 100.0 x 80.0 mm, 3 parts (0 on the bottom side), 3 nets.
