MakerWear/MakerWear/Modules/Sensor/SoundSensor/EagleDesigns/SoundSensor.brd

## EAGLE design Modules/Sensor/SoundSensor/EagleDesigns/SoundSensor.brd (2016-06-02)

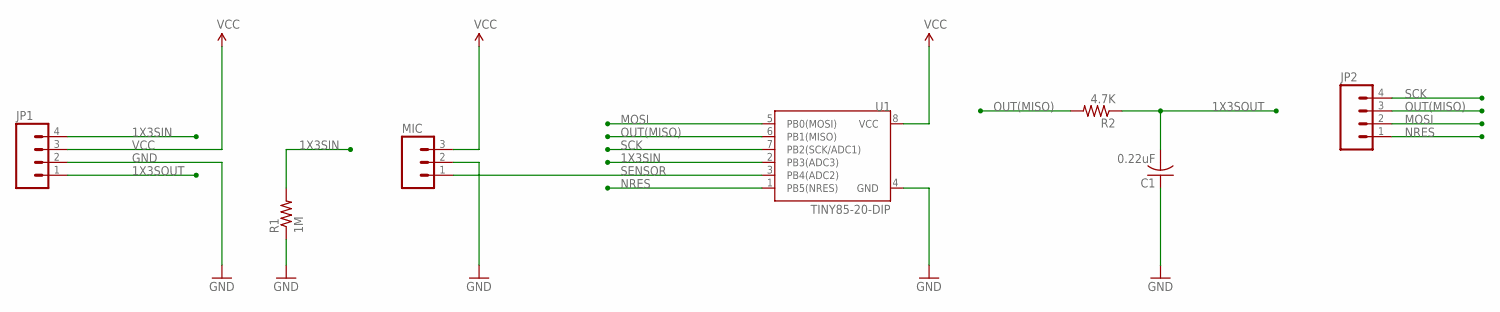
[picture p89: schematic SoundSensor.sch]

Parts:
C1: 0.22uF; C0402
JP1, JP2: M04PTH; 1X04
MIC: M03PTH; 1X03
R1: 1M; R0603
R2: 4.7K; R0603
U1: TINY85-20-DIP; DIP08

Connections:
1X3SIN: JP1.4, R1.2, U1.2 (PB3(ADC3))
1X3SOUT: C1.2, JP1.1, R2.1
GND: C1.1, JP1.2, MIC.2, R1.1, U1.4 (GND)
MOSI: JP2.2, U1.5 (PB0(MOSI))
NRES: JP2.1, U1.1 (PB5(NRES))
OUT(MISO): JP2.3, R2.2, U1.6 (PB1(MISO))
SCK: JP2.4, U1.7 (PB2(SCK/ADC1))
SENSOR: MIC.1, U1.3 (PB4(ADC2))
VCC: JP1.3, MIC.3, U1.8 (VCC)

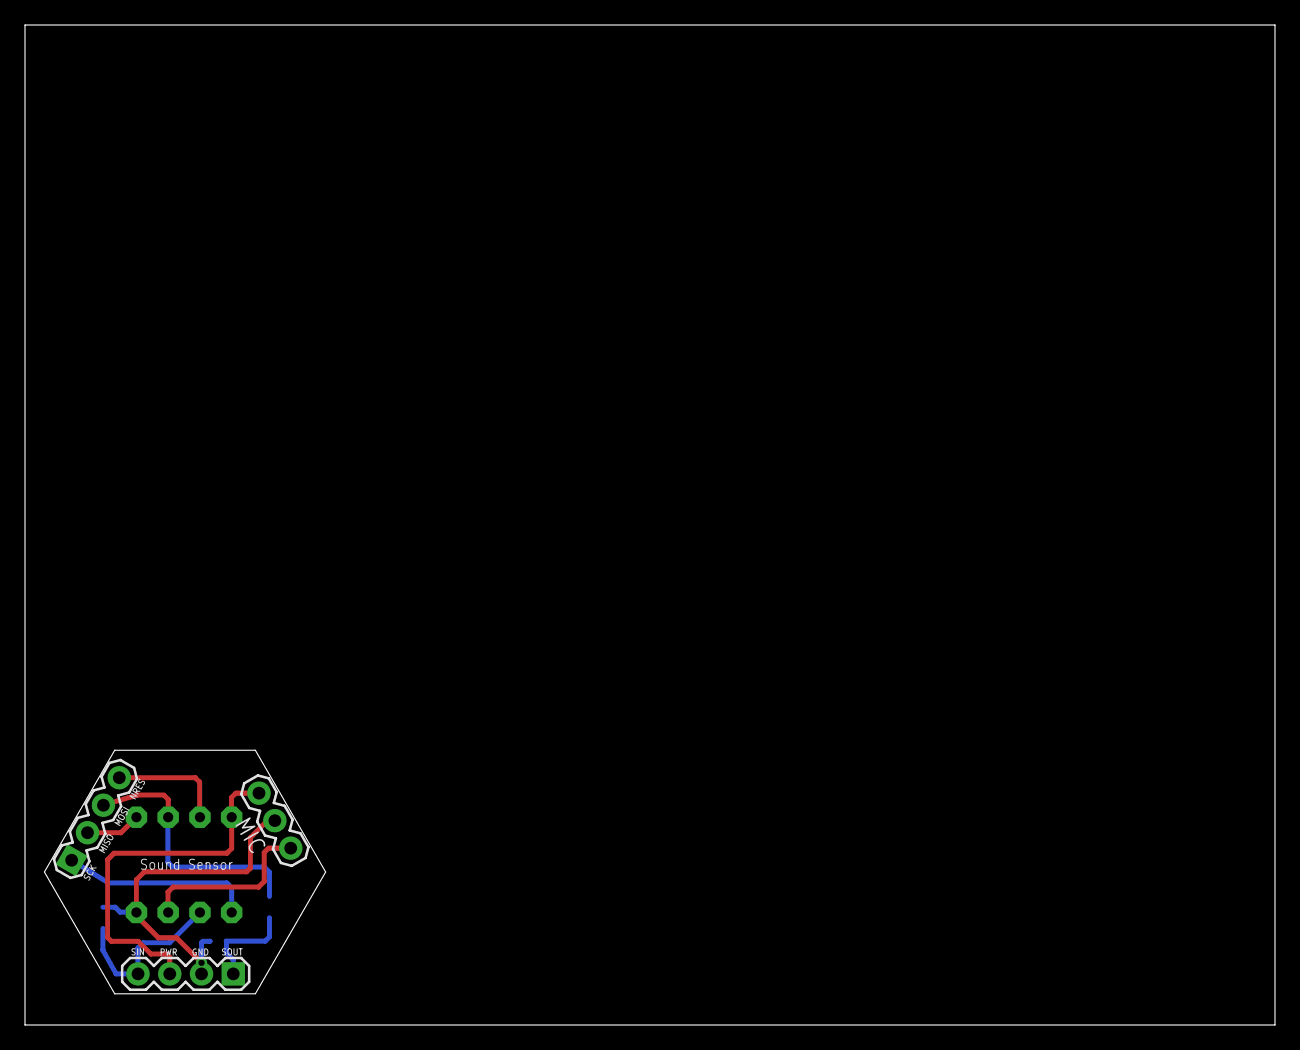
[picture p90: board SoundSensor.brd from above]

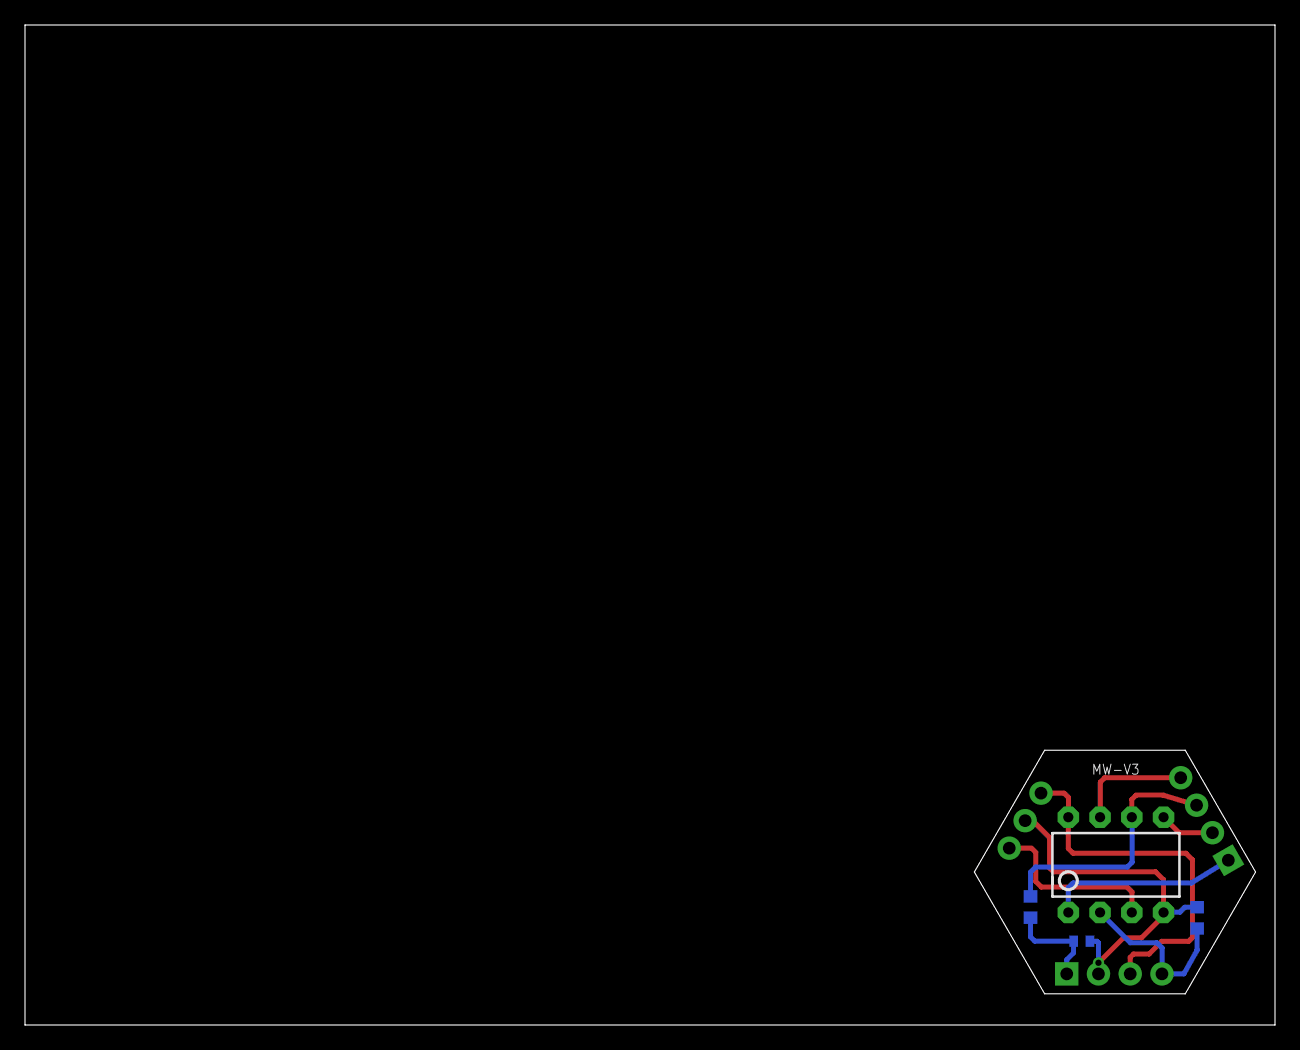
[picture p91: board SoundSensor.brd from below]

Board: 2 copper layers, 100.0 x 80.0 mm, 7 parts (4 on the bottom side), 9 nets.
