MakerWear/MakerWear/Modules/Sensor/ImpactSensor/EagleDesigns/ImpactSensor.brd

## EAGLE design Modules/Sensor/ImpactSensor/EagleDesigns/ImpactSensor.brd (2016-07-10)

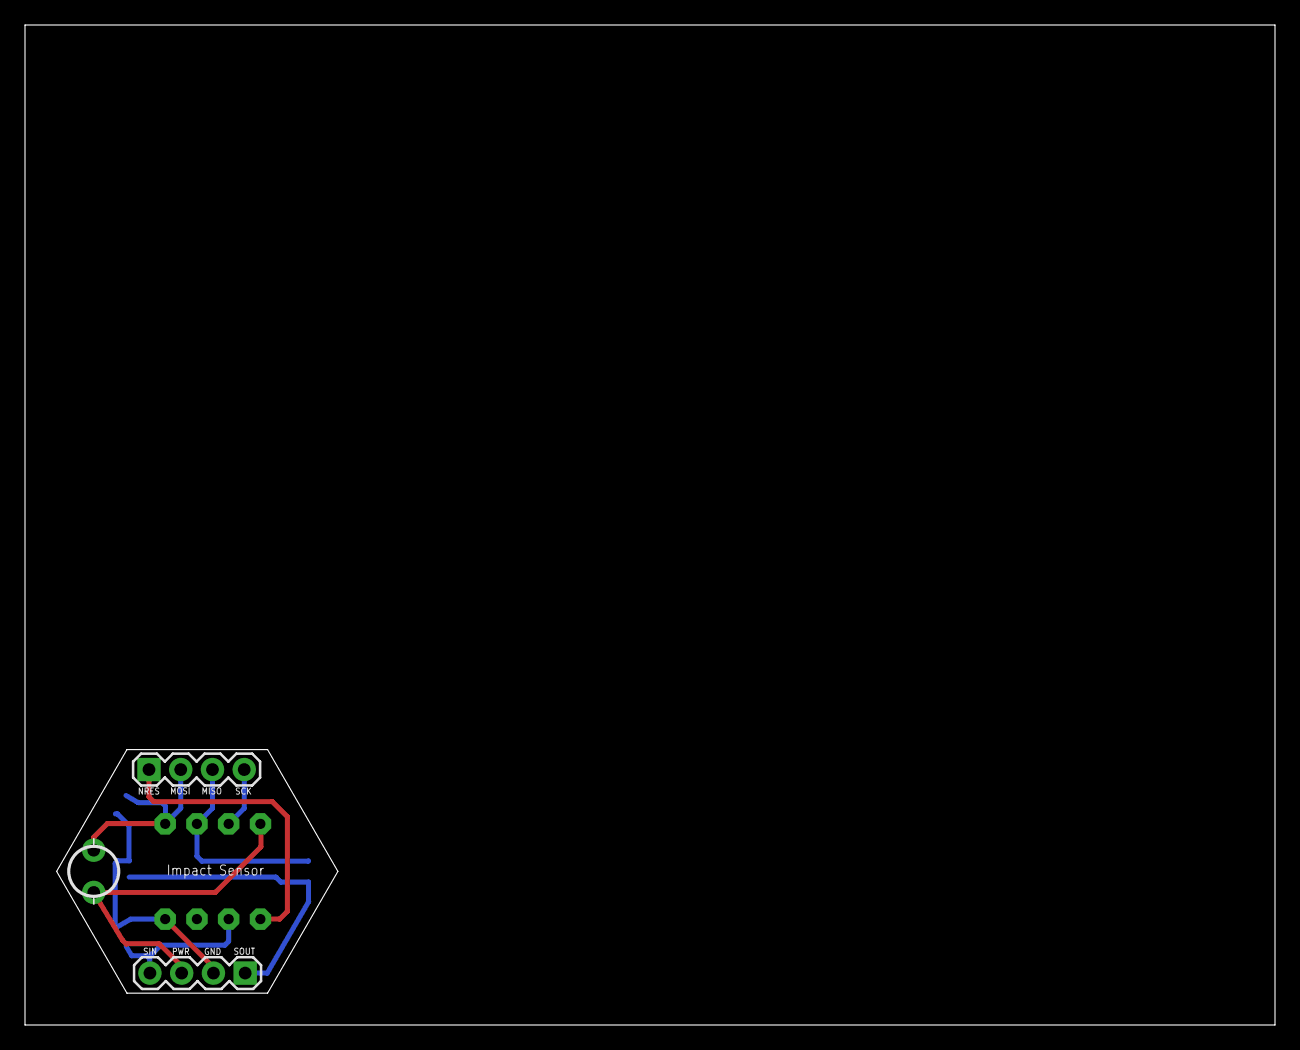
[picture p92: board ImpactSensor.brd from above]

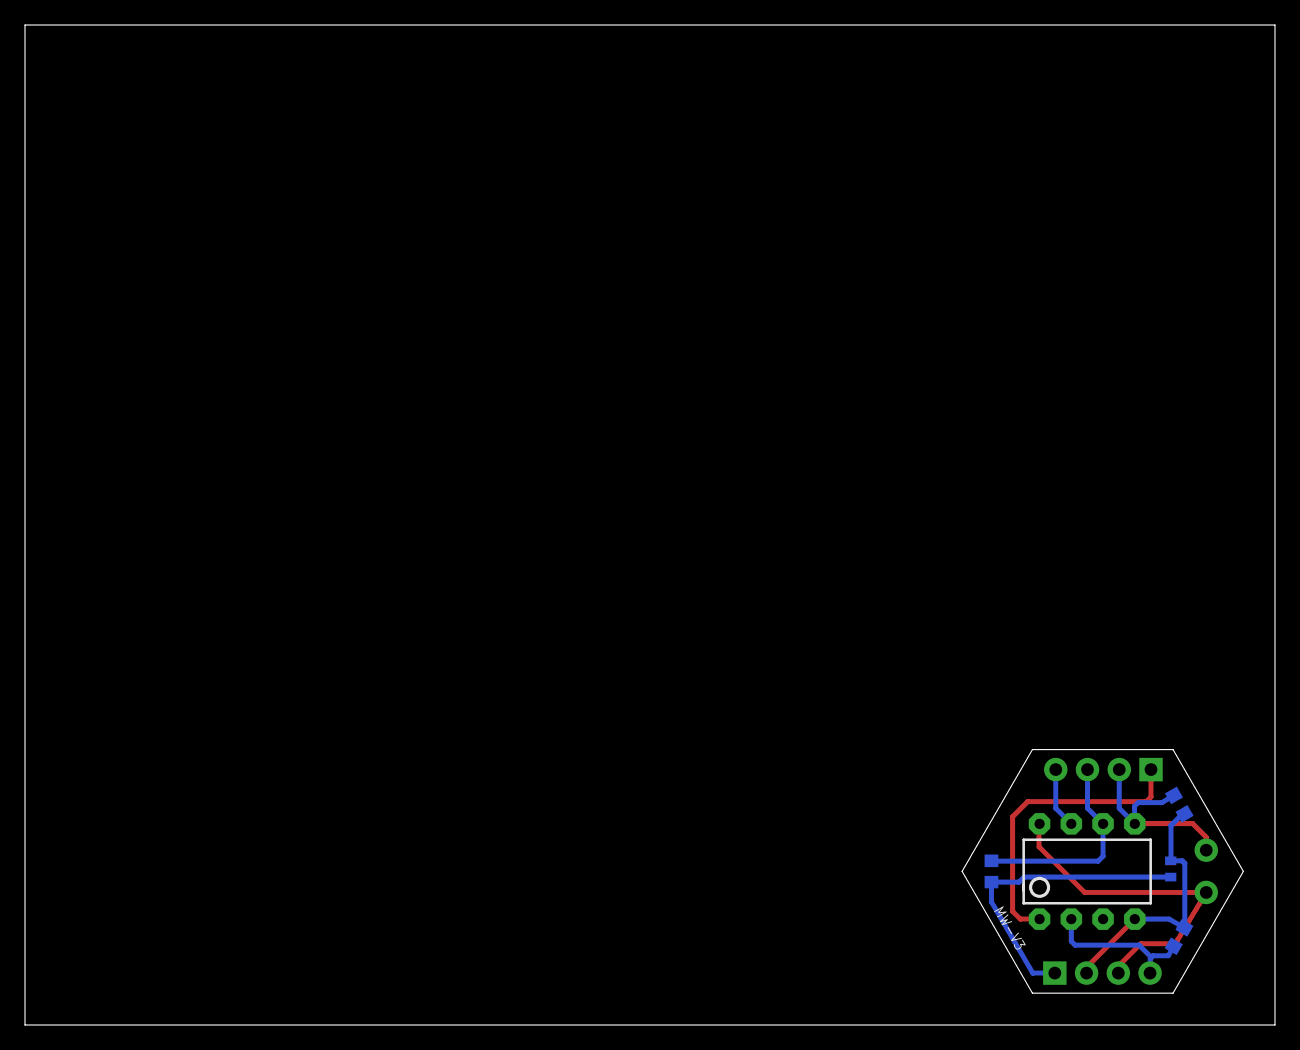
[picture p93: board ImpactSensor.brd from below]

Board: 2 copper layers, 100.0 x 80.0 mm, 8 parts (5 on the bottom side), 8 nets.

Parts:
C1: 0.22uF; C0402
JP1, JP2: 1X04
R1: 1M; R0603
R2: 330K; R0603
R3: 4.7K; R0603
TILT1: TILT-AT407
U2: TINY85-20-DIP; DIP08

Connections:
1X3SIN: JP1.4, R1.2, U2.2
1X3SOUT: C1.2, JP1.1, R3.1
GND: C1.1, JP1.2, R1.1, R2.1, U2.4
NRES: JP2.1, U2.1
OUT(MISO): JP2.3, R3.2, U2.6
SCK: JP2.4, U2.7
SENSOR(MOSI): JP2.2, R2.2, TILT1.P$2, U2.5
VCC: JP1.3, TILT1.P$1, U2.8
