MakerWear/MakerWear/Modules/Sensor/TemperatureSensor/EagleDesigns/TemperatureSensor.brd

## EAGLE design Modules/Sensor/TemperatureSensor/EagleDesigns/TemperatureSensor.brd (2016-07-10)

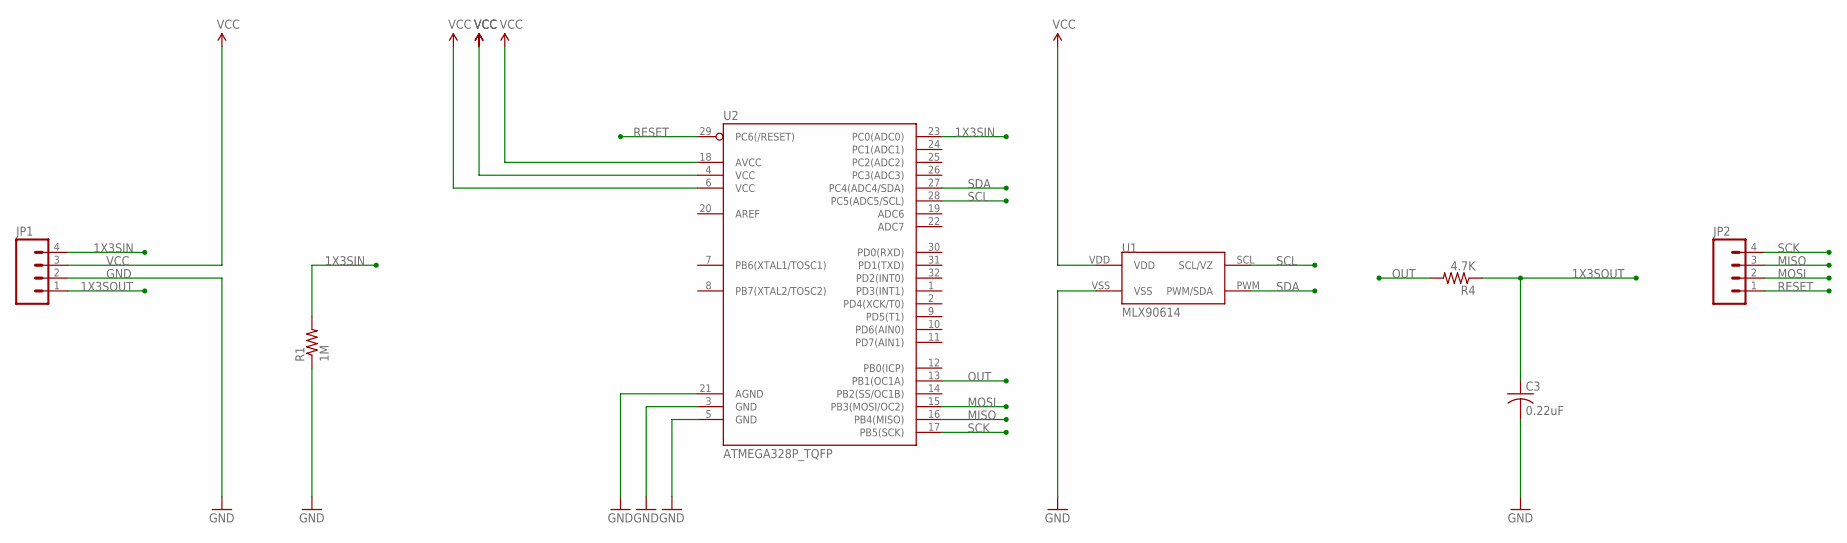
[picture p94: schematic TemperatureSensor.sch]

Parts:
C3: 0.22uF; C0603
JP1, JP2: M04PTH; 1X04
R1: 1M; R0603
R4: 4.7K; R0603
U1: MLX90614; TO-39
U2: ATMEGA328P_TQFP; TQFP32-08

Connections:
1X3SIN: JP1.4, R1.2, U2.23 (PC0(ADC0))
1X3SOUT: C3.1, JP1.1, R4.1
GND: C3.2, JP1.2, R1.1, U1.VSS, U2.3 (GND), U2.5 (GND), U2.21 (AGND)
MISO: JP2.3, U2.16 (PB4(MISO))
MOSI: JP2.2, U2.15 (PB3(MOSI/OC2))
OUT: R4.2, U2.13 (PB1(OC1A))
RESET: JP2.1, U2.29 (PC6(/RESET))
SCK: JP2.4, U2.17 (PB5(SCK))
SCL: U1.SCL (SCL/VZ), U2.28 (PC5(ADC5/SCL))
SDA: U1.PWM (PWM/SDA), U2.27 (PC4(ADC4/SDA))
VCC: JP1.3, U1.VDD, U2.4 (VCC), U2.6 (VCC), U2.18 (AVCC)

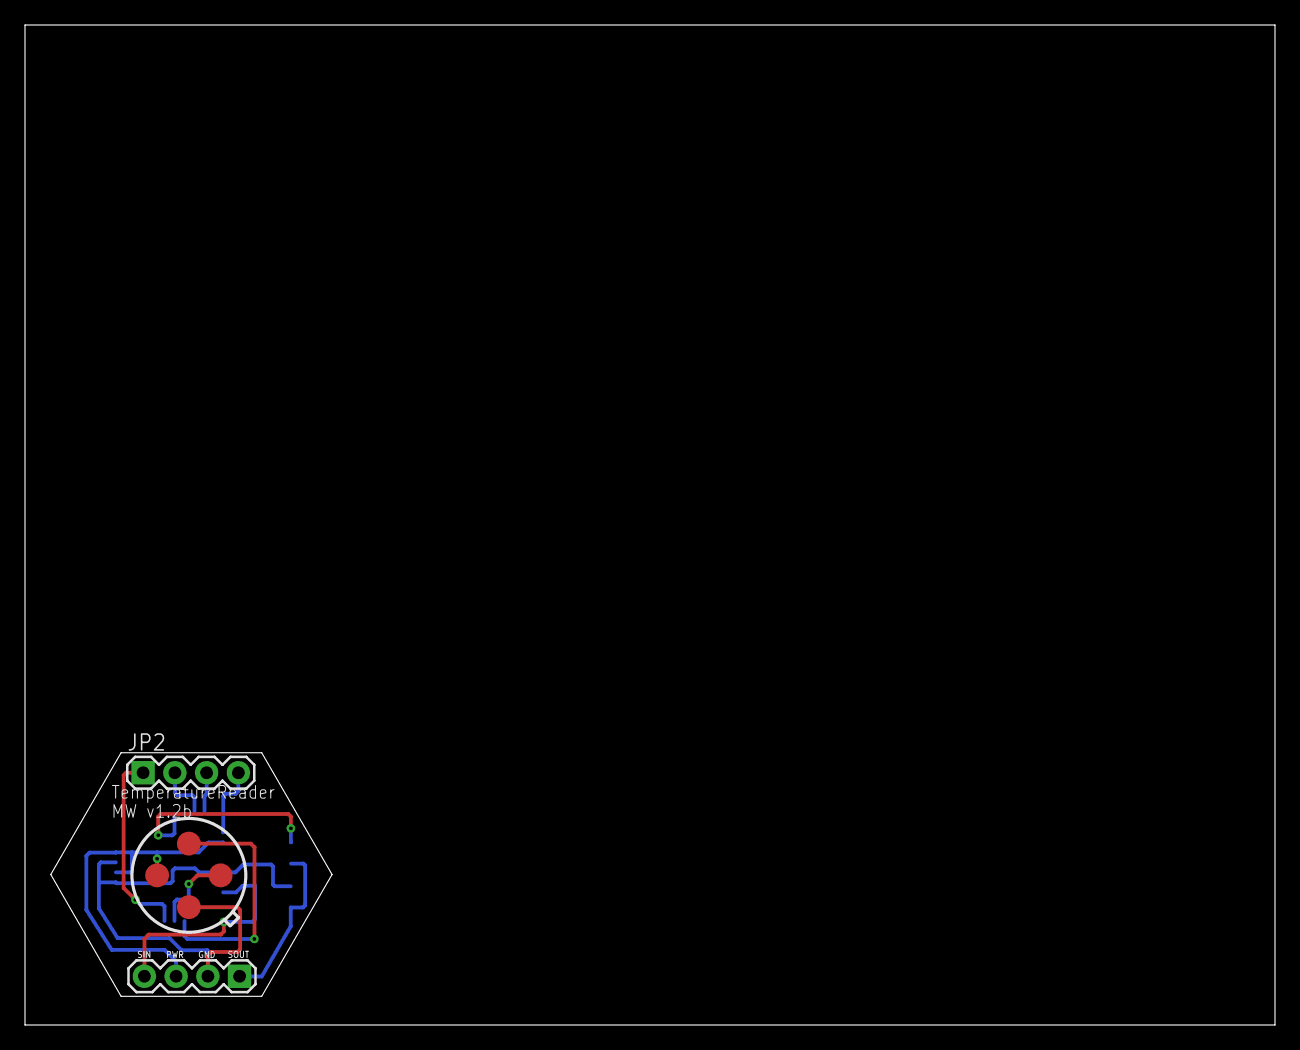
[picture p95: board TemperatureSensor.brd from above]

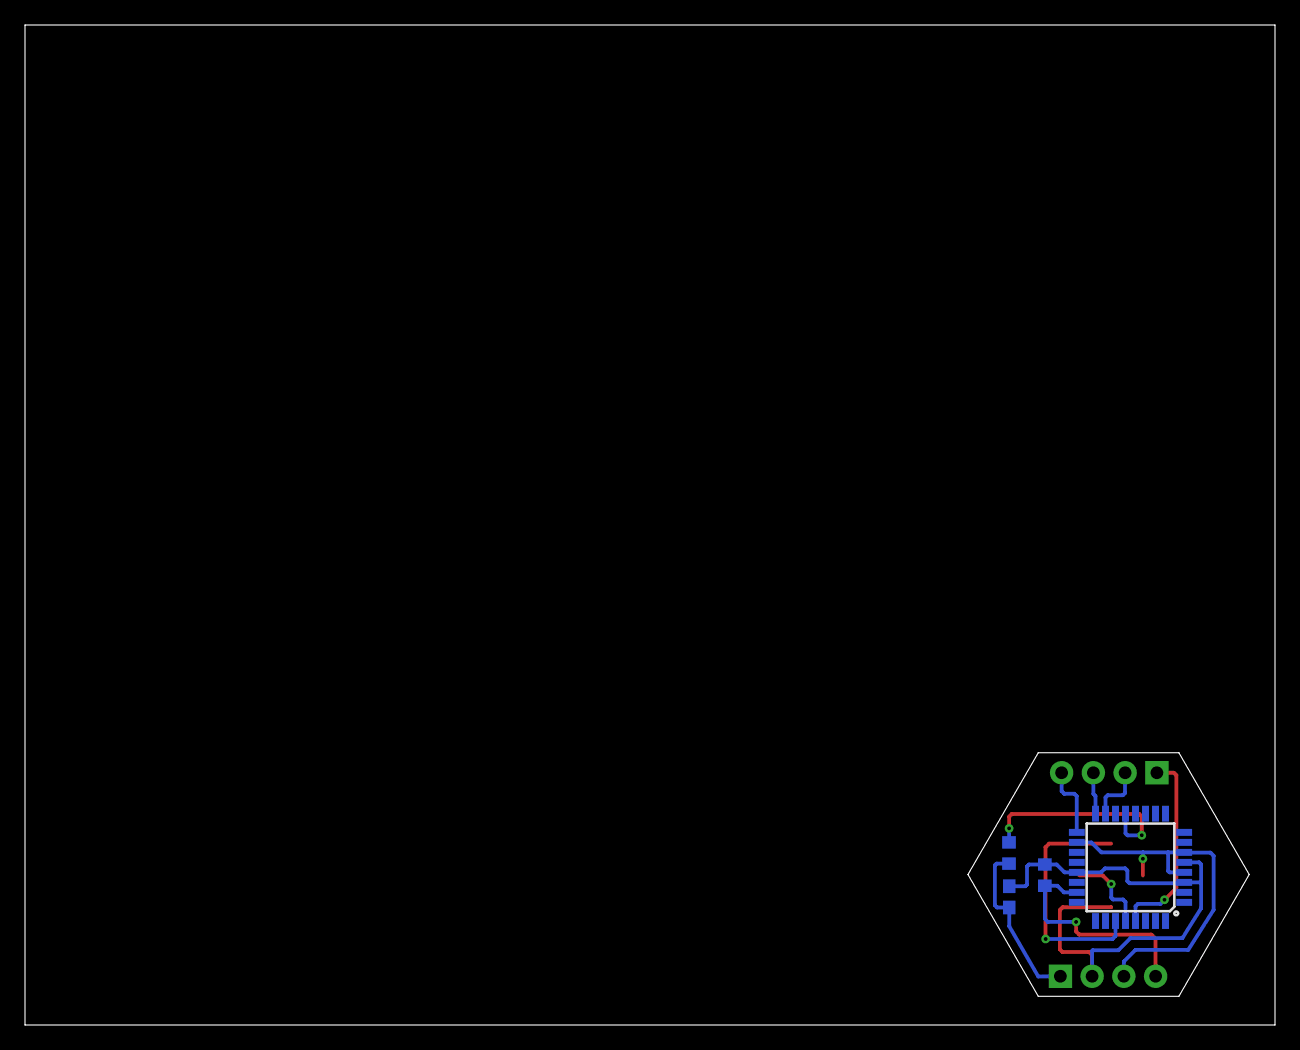
[picture p96: board TemperatureSensor.brd from below]

Board: 2 copper layers, 100.0 x 80.0 mm, 7 parts (4 on the bottom side), 11 nets.
