MakerWear/MakerWear/Common/ProgrammerShields/ATmegaExtOscillator/ATmegaExtOscillator.brd

## EAGLE design Common/ProgrammerShields/ATmegaExtOscillator/ATmegaExtOscillator.brd (2016-06-27)

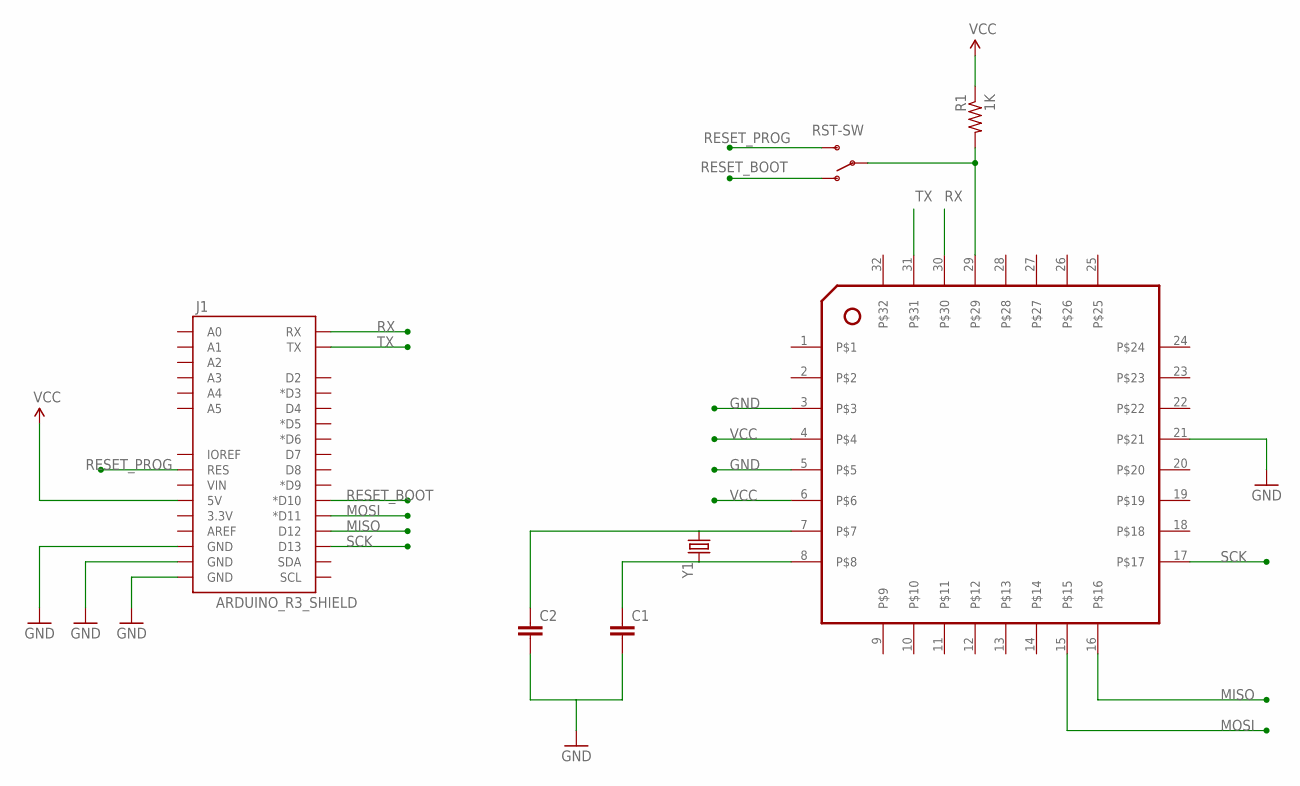
[picture p97: schematic ATmegaExtOscillator.sch]

Parts:
C1, C2: 0.1UF-50V-20%(PTH)KIT-EZ; CAP-PTH-SMALL-KIT
J1: ARDUINO_R3_SHIELD; UNO_R3_SHIELD
R1: 1K; AXIAL-0.3
RST-SW: SWITCH-SPDTPTH; SWITCH-SPDT
U$1: ATMEGA-TQFP-BREAKOUT; TQFP32-BREAKOUT
Y1: CRYSTALHC49US; HC49US

Connections:
GND: C1.2, C2.2, J1.GND@0 (GND), J1.GND@1 (GND), J1.GND@2 (GND), U$1.3, U$1.5, U$1.21
MISO: J1.D12, U$1.16
MOSI: J1.D11 (*D11), U$1.15
unnamed: C2.1, U$1.7, Y1.1
unnamed: C1.1, U$1.8, Y1.2
RESET: R1.P$2 (2), RST-SW.2, U$1.29
RESET_BOOT: J1.D10 (*D10), RST-SW.1 (O)
RESET_PROG: J1.RES, RST-SW.3 (S)
RX: J1.RX, U$1.30
SCK: J1.D13, U$1.17
TX: J1.TX, U$1.31
VCC: J1.5V, R1.P$1 (1), U$1.4, U$1.6

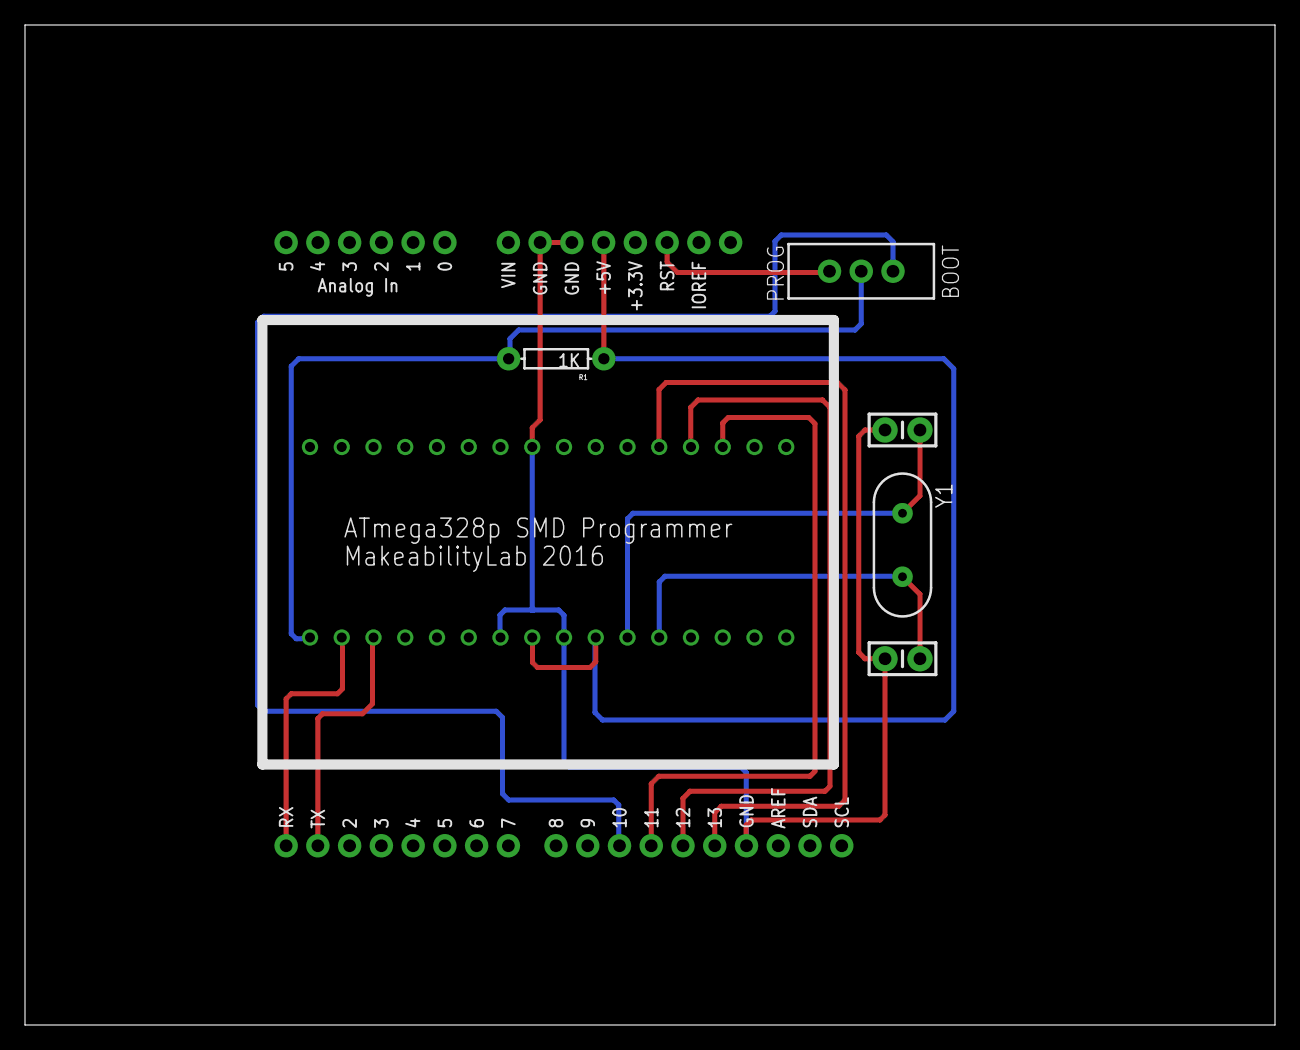
[picture p98: board ATmegaExtOscillator.brd from above]

Board: 2 copper layers, 100.0 x 80.0 mm, 7 parts (0 on the bottom side), 12 nets.
