MakerWear/MakerWear/Modules/Sensor/DistanceSensor/EagleDesigns/DistanceSensor.brd

## EAGLE design Modules/Sensor/DistanceSensor/EagleDesigns/DistanceSensor.brd (2016-07-10)

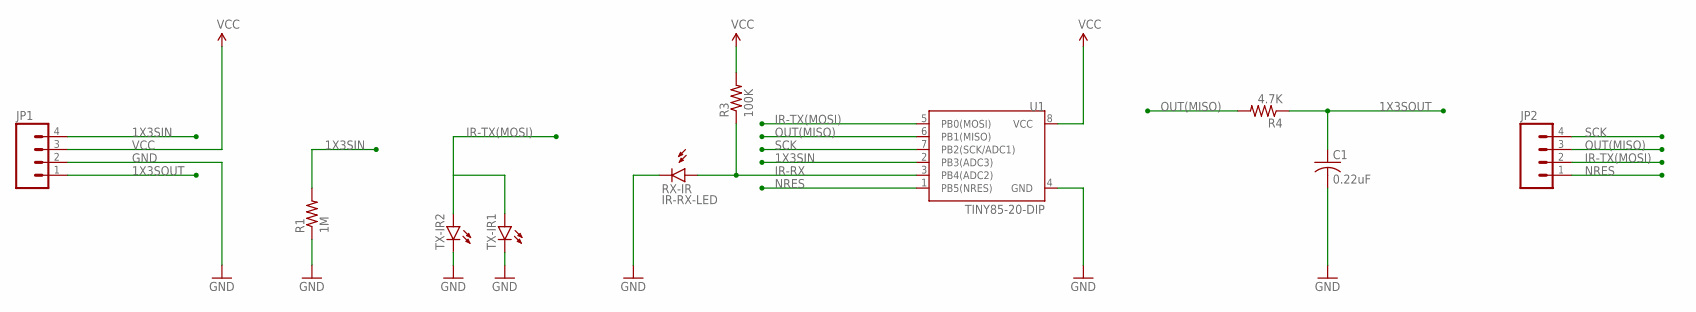
[picture p99: schematic DistanceSensor.sch]

Parts:
C1: 0.22uF; C0603
JP1, JP2: M04PTH; 1X04
R1: 1M; R0603
R3: 100K; R0603
R4: 4.7K; R0603
RX-IR: IR-RX-LED; LED5MM
TX-IR1, TX-IR2: LED5MM
U1: TINY85-20-DIP; DIP08

Connections:
1X3SIN: JP1.4, R1.2, U1.2 (PB3(ADC3))
1X3SOUT: C1.1, JP1.1, R4.1
GND: C1.2, JP1.2, R1.1, RX-IR.K (C), TX-IR1.K (C), TX-IR2.K (C), U1.4 (GND)
IR-RX: R3.1, RX-IR.A, U1.3 (PB4(ADC2))
IR-TX(MOSI): JP2.2, TX-IR1.A, TX-IR2.A, U1.5 (PB0(MOSI))
NRES: JP2.1, U1.1 (PB5(NRES))
OUT(MISO): JP2.3, R4.2, U1.6 (PB1(MISO))
SCK: JP2.4, U1.7 (PB2(SCK/ADC1))
VCC: JP1.3, R3.2, U1.8 (VCC)

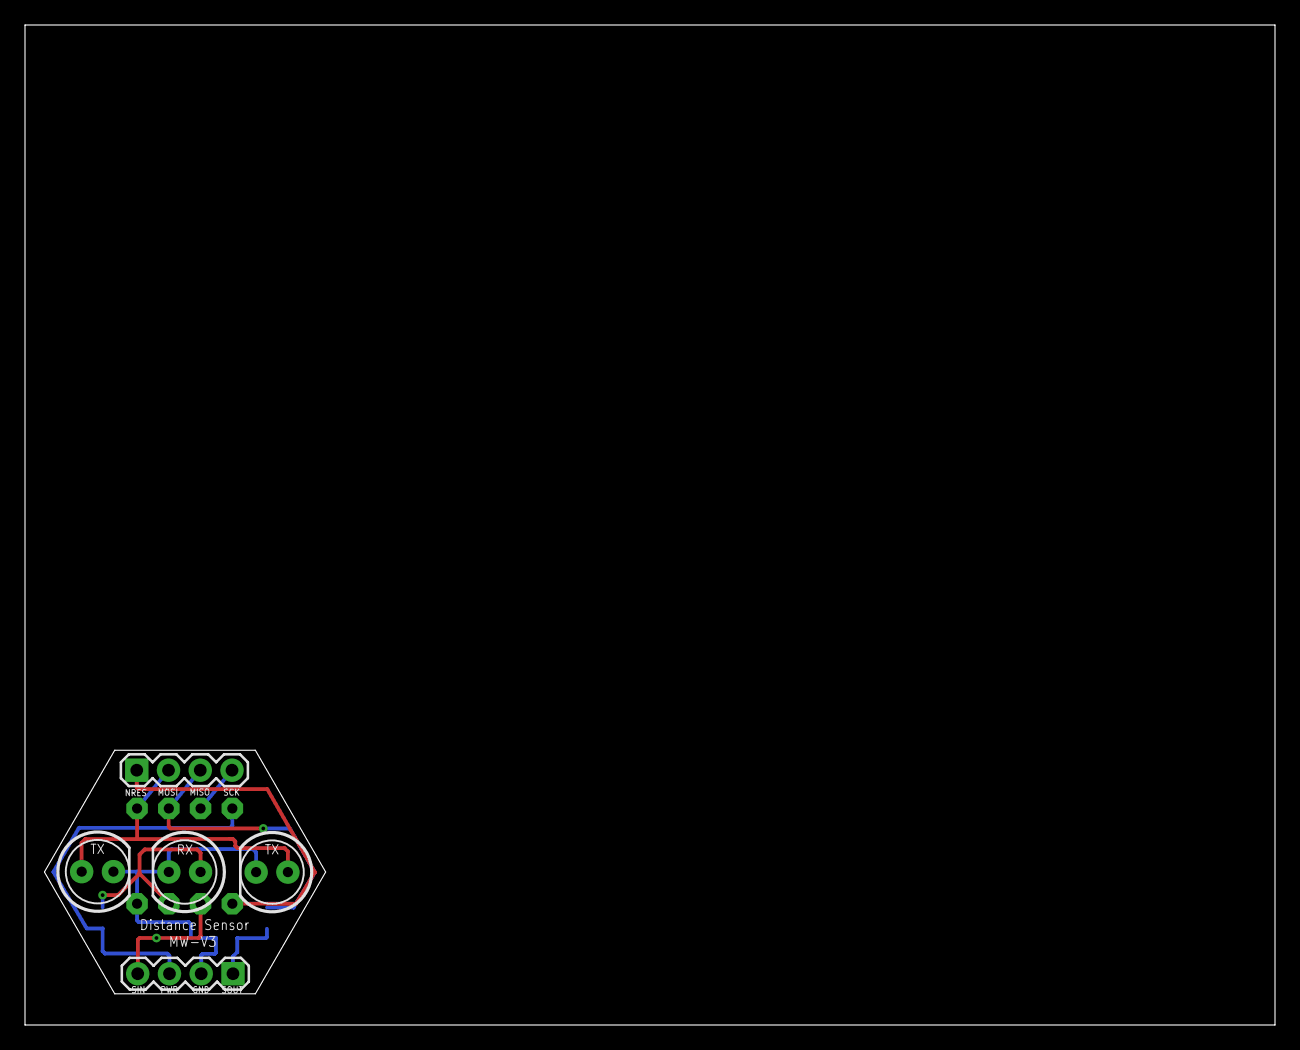
[picture p100: board DistanceSensor.brd from above]

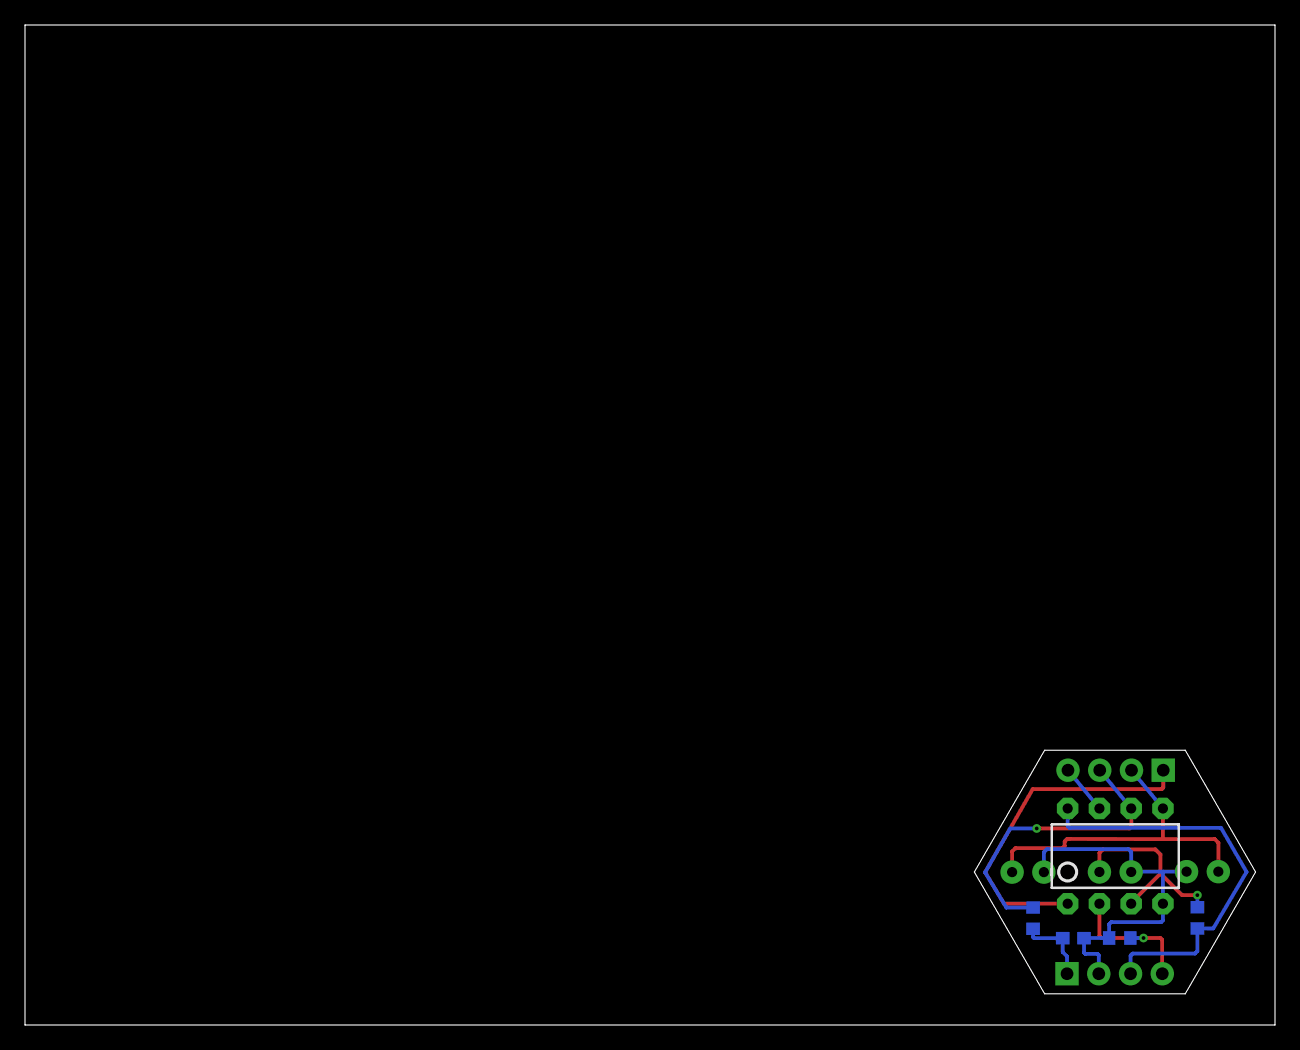
[picture p101: board DistanceSensor.brd from below]

Board: 2 copper layers, 100.0 x 80.0 mm, 10 parts (5 on the bottom side), 9 nets.
