MakerWear/MakerWear/Modules/Action/Number/EagleDesigns/Number.brd

## EAGLE design Modules/Action/Number/EagleDesigns/Number.brd (2016-07-10)

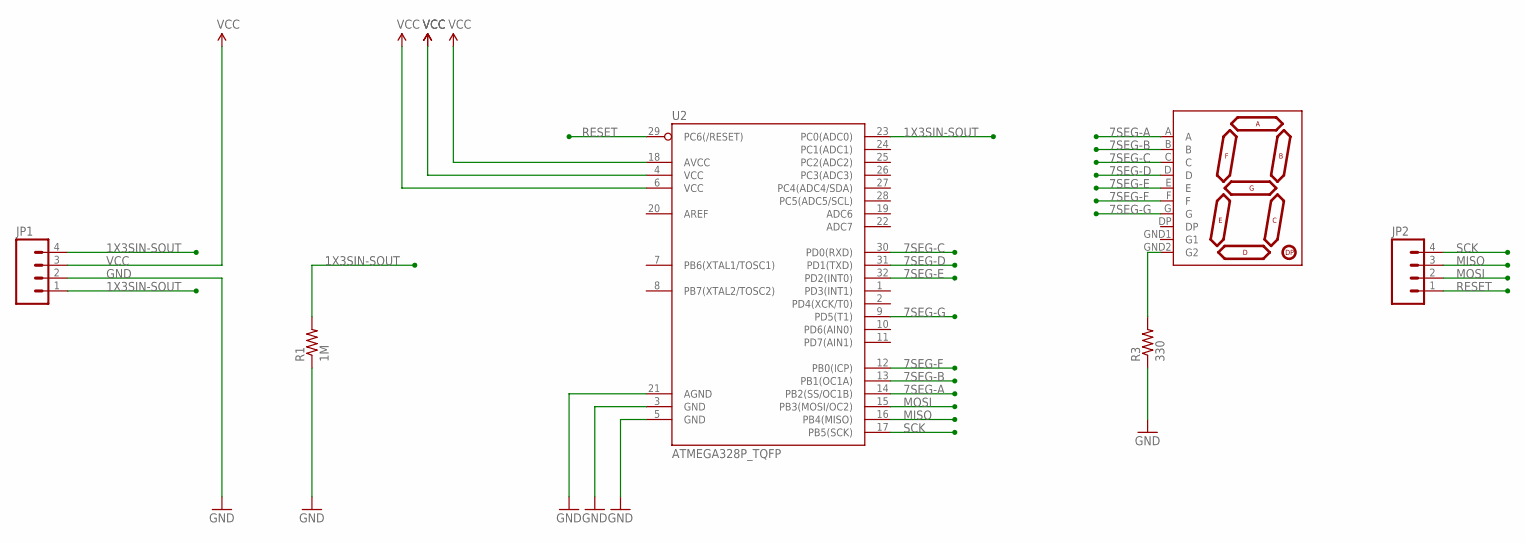
[picture p102: schematic Number.sch]

Parts:
JP1, JP2: M04PTH; 1X04
R1: 1M; R0603
R3: 330; R0603
U2: ATMEGA328P_TQFP; TQFP32-08
U$1: 7SEGMENT; 7SEG-SMD-10X7.3

Connections:
1X3SIN-SOUT: JP1.1, JP1.4, R1.2, U2.23 (PC0(ADC0))
7SEG-A: U2.14 (PB2(SS/OC1B)), U$1.A
7SEG-B: U2.13 (PB1(OC1A)), U$1.B
7SEG-C: U2.30 (PD0(RXD)), U$1.C
7SEG-D: U2.31 (PD1(TXD)), U$1.D
7SEG-E: U2.32 (PD2(INT0)), U$1.E
7SEG-F: U2.12 (PB0(ICP)), U$1.F
7SEG-G: U2.9 (PD5(T1)), U$1.G
GND: JP1.2, R1.1, R3.1, U2.3 (GND), U2.5 (GND), U2.21 (AGND)
MISO: JP2.3, U2.16 (PB4(MISO))
MOSI: JP2.2, U2.15 (PB3(MOSI/OC2))
unnamed: R3.2, U$1.GND2 (G2)
RESET: JP2.1, U2.29 (PC6(/RESET))
SCK: JP2.4, U2.17 (PB5(SCK))
VCC: JP1.3, U2.4 (VCC), U2.6 (VCC), U2.18 (AVCC)
