MakerWear/MakerWear/Modules/Action/Number/EagleDesigns/Number.brd

## EAGLE design Modules/Action/Number/EagleDesigns/Number.brd (continued)

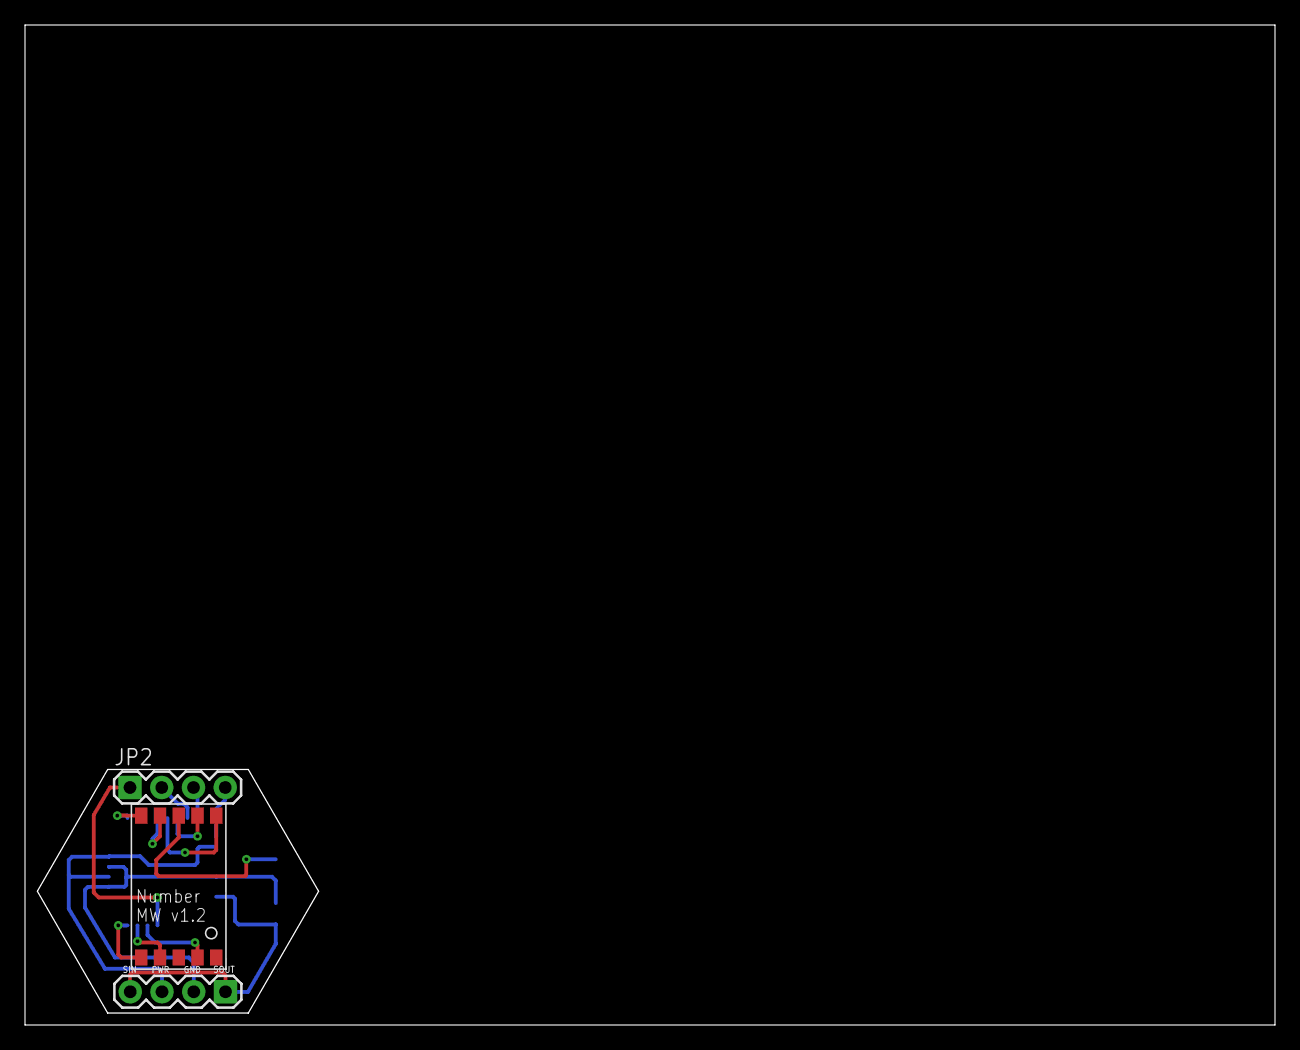
[picture p103: board Number.brd from above]

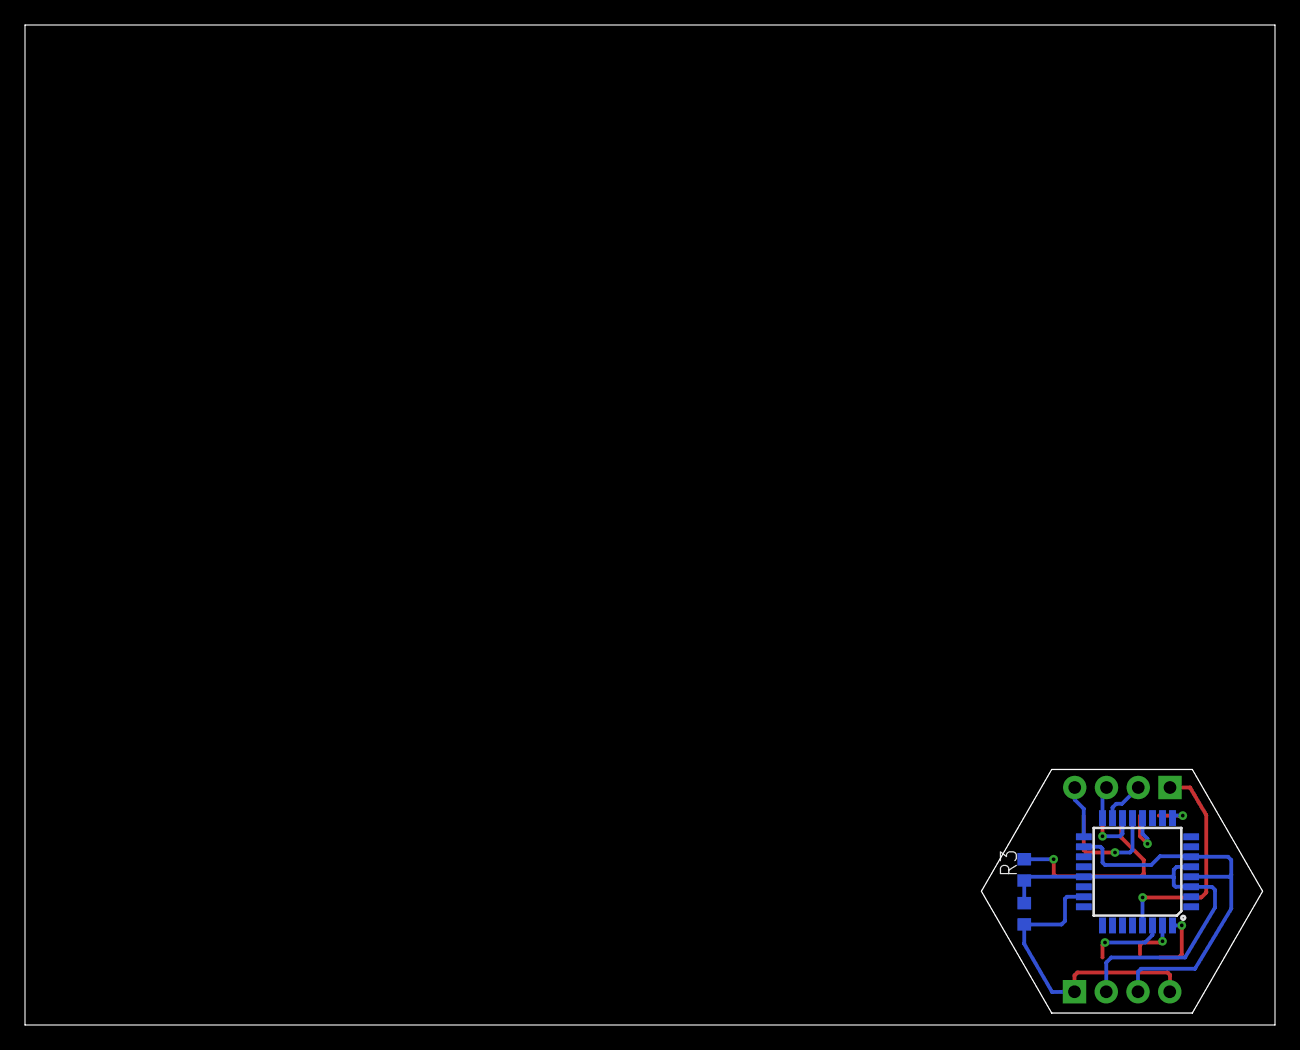
[picture p104: board Number.brd from below]

Board: 2 copper layers, 100.0 x 80.0 mm, 6 parts (3 on the bottom side), 15 nets.
