MakerWear/MakerWear/Common/ProgrammerShields/ATtinyProgrammer/ATtinyProgrammer.brd

## EAGLE design Common/ProgrammerShields/ATtinyProgrammer/ATtinyProgrammer.brd (2016-06-17)

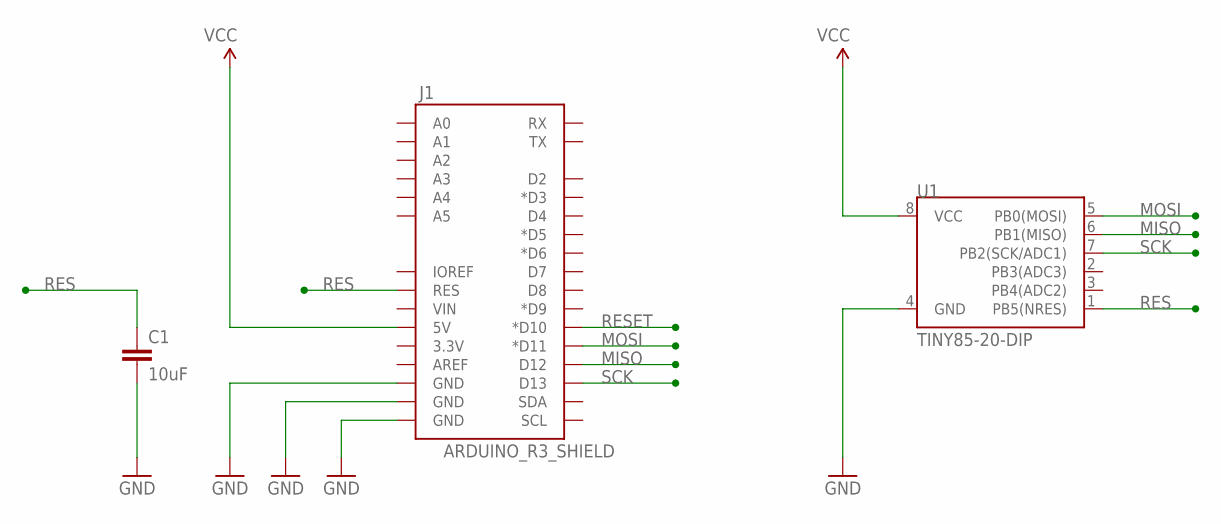
[picture p108: schematic ATtinyProgrammer.sch]

Parts:
C1: 10uF; CAP-PTH-SMALL-KIT
J1: ARDUINO_R3_SHIELD; UNO_R3_SHIELD
U1: TINY85-20-DIP; DIP08

Connections:
GND: C1.2, J1.GND@0 (GND), J1.GND@1 (GND), J1.GND@2 (GND), U1.4 (GND)
MISO: J1.D12, U1.6 (PB1(MISO))
MOSI: J1.D11 (*D11), U1.5 (PB0(MOSI))
RES: C1.1, J1.RES, U1.1 (PB5(NRES))
RESET: J1.D10 (*D10)
SCK: J1.D13, U1.7 (PB2(SCK/ADC1))
VCC: J1.5V, U1.8 (VCC)

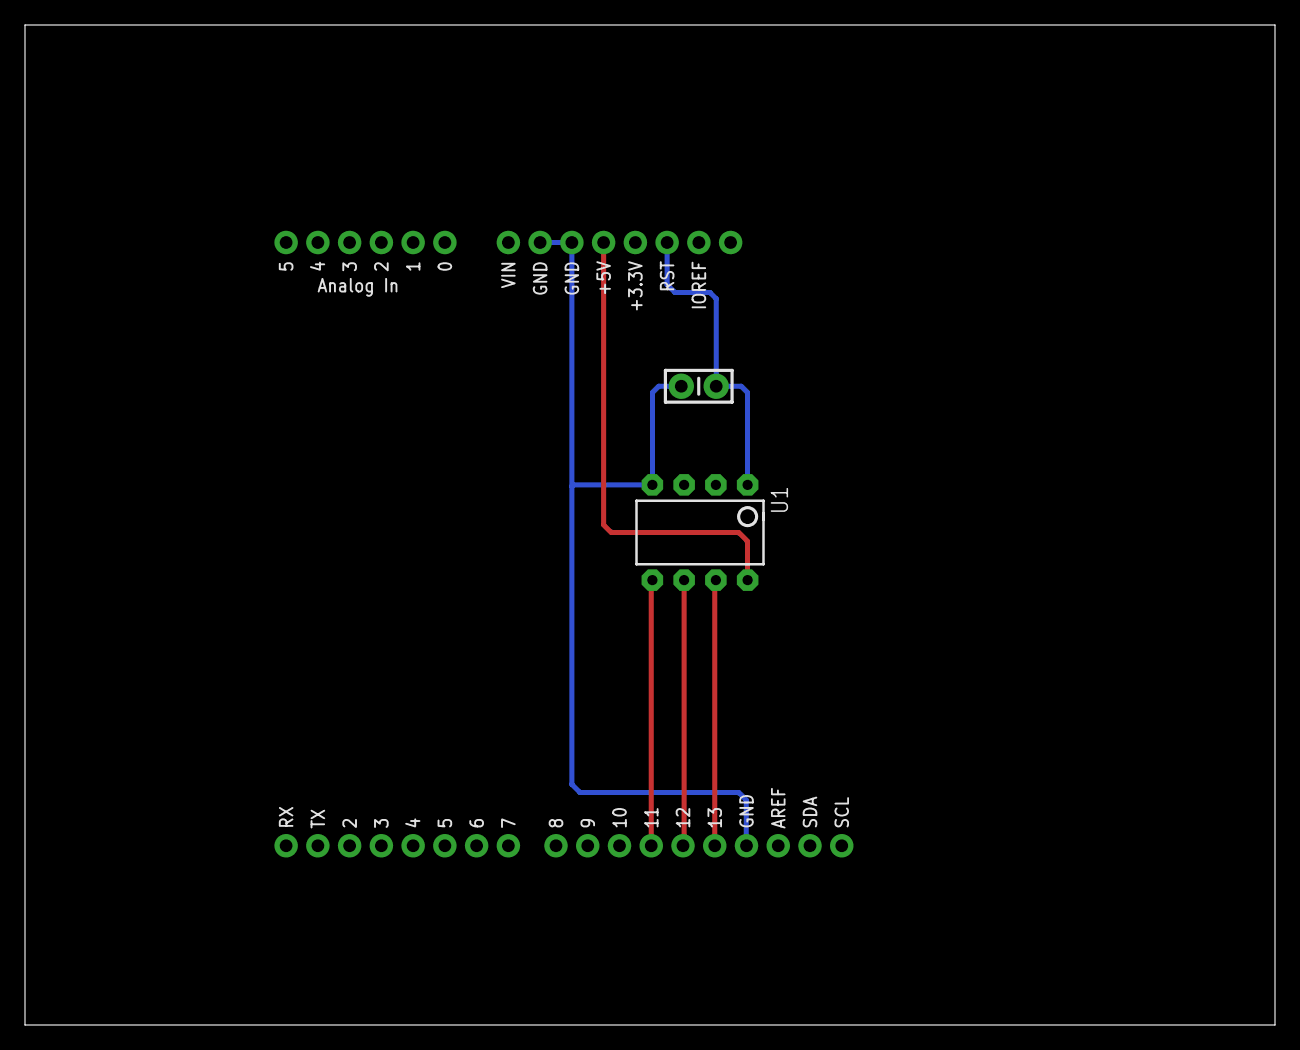
[picture p109: board ATtinyProgrammer.brd from above]

Board: 2 copper layers, 100.0 x 80.0 mm, 3 parts (0 on the bottom side), 6 nets.
