MakerWear/MakerWear/Modules/Power/EagleDesigns/Power.brd

## EAGLE design Modules/Power/EagleDesigns/Power.brd (2016-06-02)

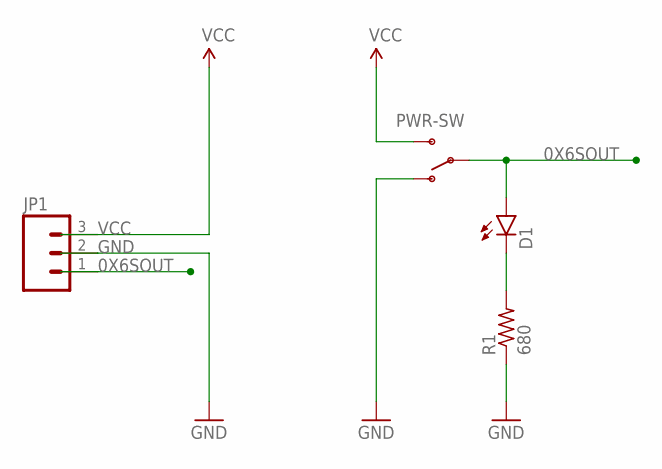
[picture p113: schematic Power.sch]

Parts:
D1: LED3MM
JP1: M03PTH; 1X03
PWR-SW: SWITCH-SPDTPTH; SWITCH-SPDT
R1: 680; R0603

Connections:
0X6SOUT: D1.A, JP1.1, PWR-SW.2
CUR-LIMIT-LED: D1.K (C), R1.2
GND: JP1.2, PWR-SW.1 (O), R1.1
VCC: JP1.3, PWR-SW.3 (S)

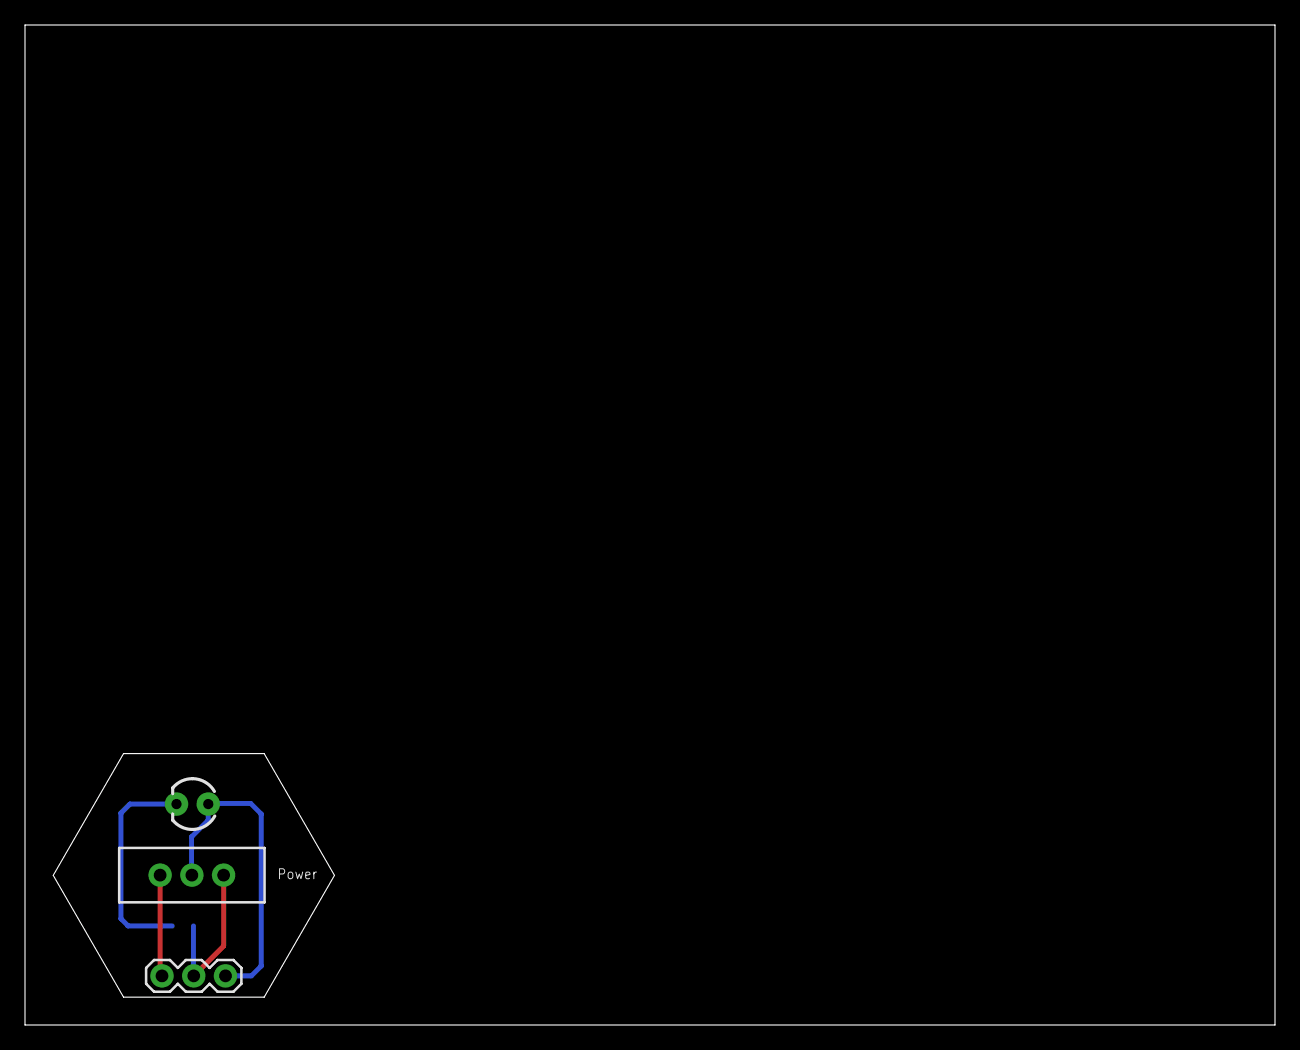
[picture p114: board Power.brd from above]

Board: 2 copper layers, 100.0 x 80.0 mm, 4 parts (1 on the bottom side), 4 nets.
