MakerWear/MakerWear/Modules/Action/MultiColorLight/EagleDesigns/MultiColorLight.brd

## EAGLE design Modules/Action/MultiColorLight/EagleDesigns/MultiColorLight.brd (2016-06-02)

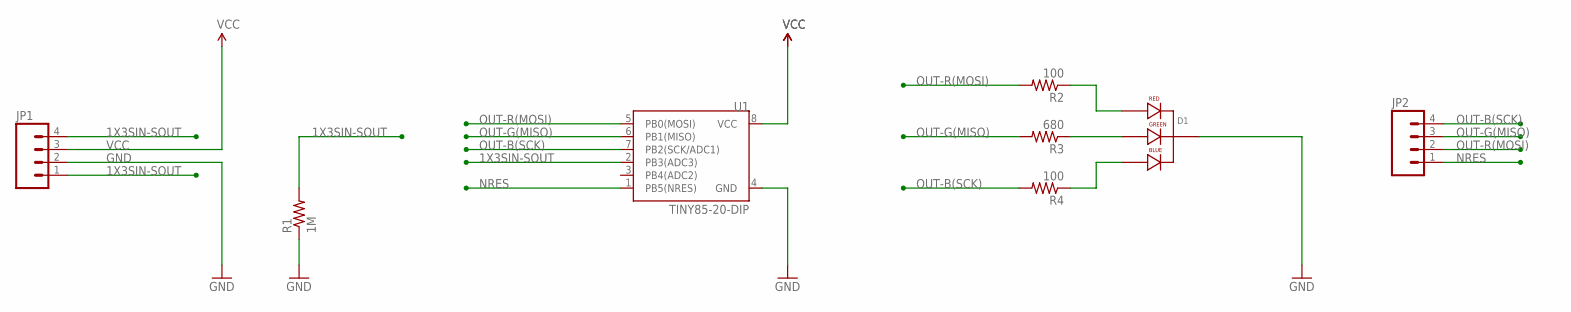
[picture p115: schematic MultiColorLight.sch]

Parts:
D1: LED-RGB-CC-THRUCLEAR; LED-RGB-THRU
JP1, JP2: M04PTH; 1X04
R1: 1M; R0603
R2, R4: 100; R0603
R3: 680; R0603
U1: TINY85-20-DIP; DIP08

Connections:
1X3SIN-SOUT: JP1.1, JP1.4, R1.2, U1.2 (PB3(ADC3))
GND: D1.2 (CATHODE), JP1.2, R1.1, U1.4 (GND)
unnamed: D1.1 (RED_CATHODE), R2.1
unnamed: D1.3 (GREEN_CATHODE), R3.1
unnamed: D1.4 (BLUE_CATHODE), R4.1
NRES: JP2.1, U1.1 (PB5(NRES))
OUT-B(SCK): JP2.4, R4.2, U1.7 (PB2(SCK/ADC1))
OUT-G(MISO): JP2.3, R3.2, U1.6 (PB1(MISO))
OUT-R(MOSI): JP2.2, R2.2, U1.5 (PB0(MOSI))
VCC: JP1.3, U1.8 (VCC)

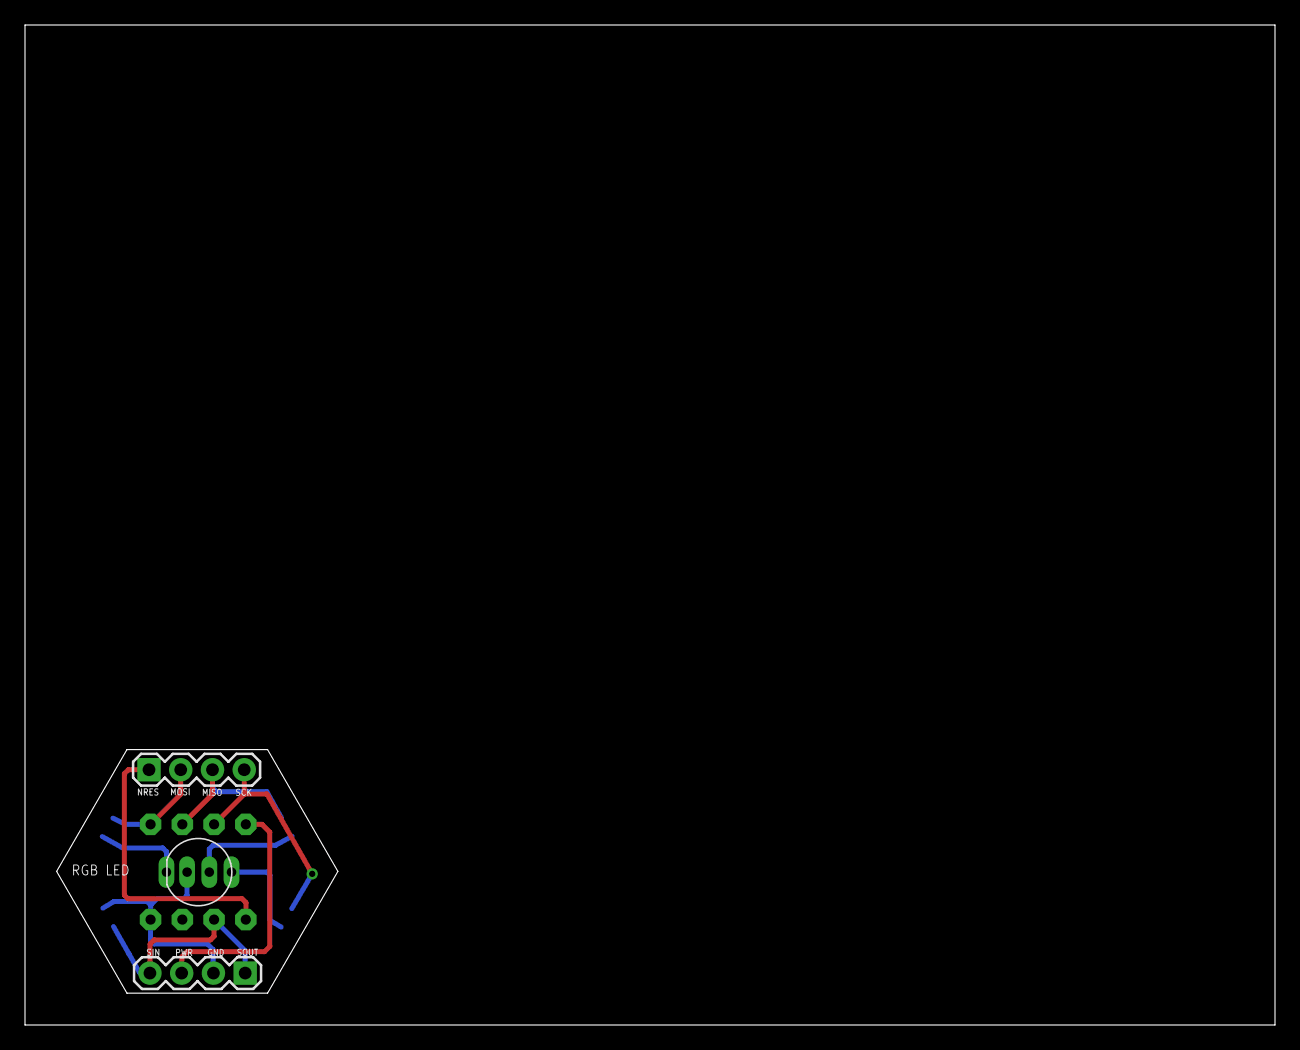
[picture p116: board MultiColorLight.brd from above]

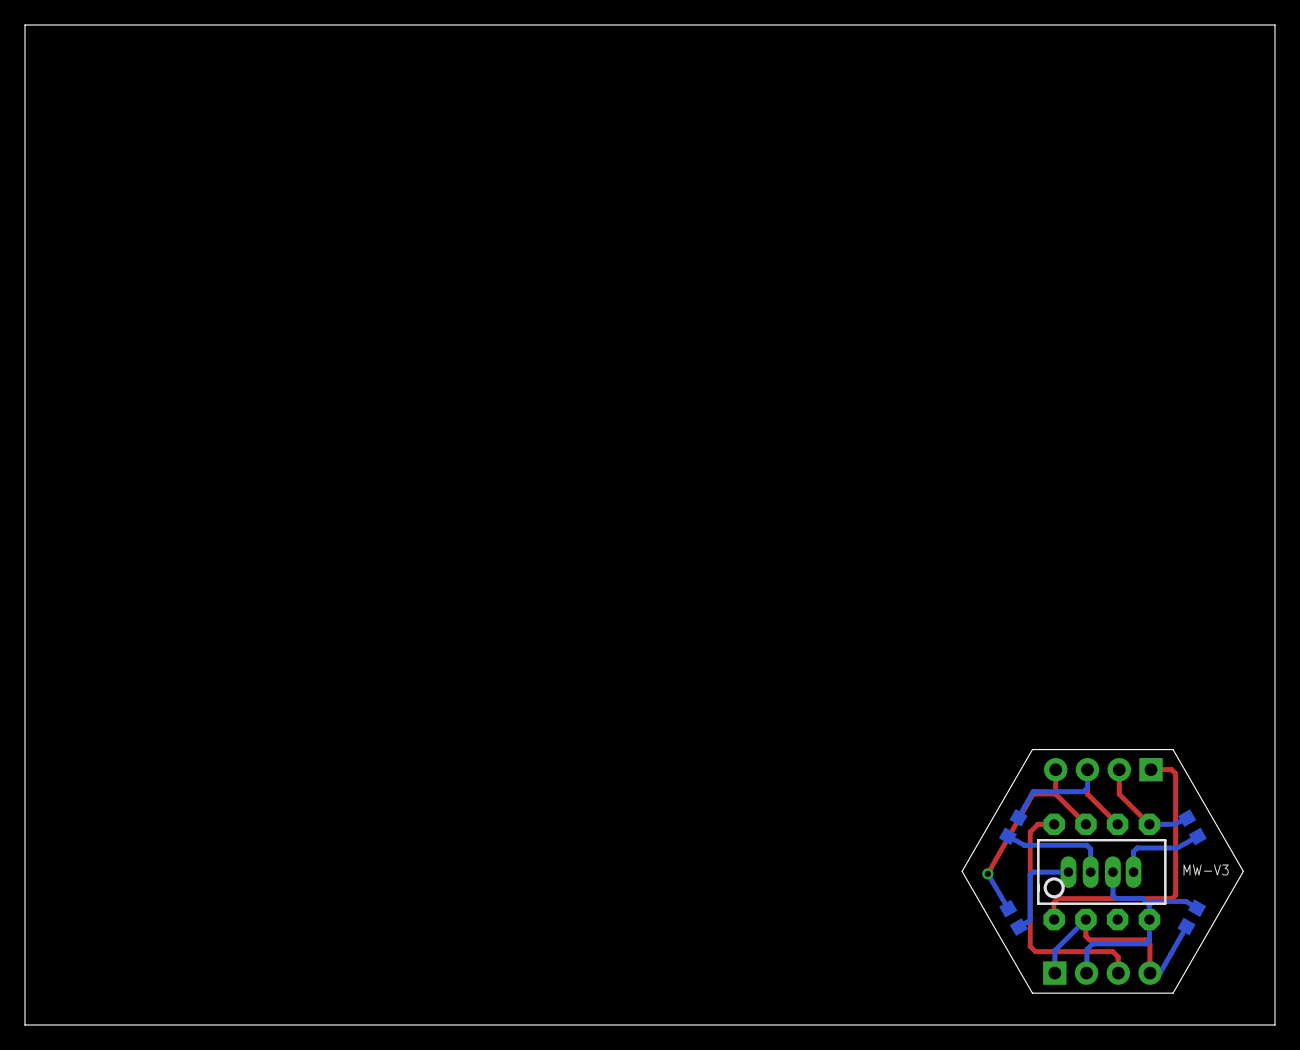
[picture p117: board MultiColorLight.brd from below]

Board: 2 copper layers, 100.0 x 80.0 mm, 8 parts (5 on the bottom side), 10 nets.
