MakerWear/MakerWear/Common/BasePCBs/1x3Top/1x3Top.sch

## EAGLE design Common/BasePCBs/1x3Top/1x3Top.sch (2016-06-12)

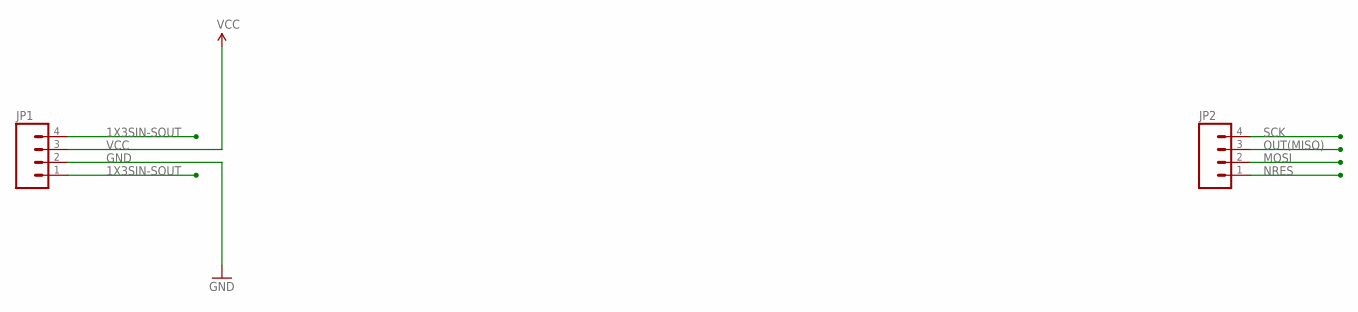
[picture p118: schematic 1x3Top.sch]

Parts:
JP1, JP2: M04PTH; 1X04

Connections:
1X3SIN-SOUT: JP1.1, JP1.4
GND: JP1.2
MOSI: JP2.2
NRES: JP2.1
OUT(MISO): JP2.3
SCK: JP2.4
VCC: JP1.3
