MakerWear/MakerWear/Modules/Action/LightBar/EagleDesigns/LightBar.sch

## EAGLE design Modules/Action/LightBar/EagleDesigns/LightBar.sch (2016-06-02)

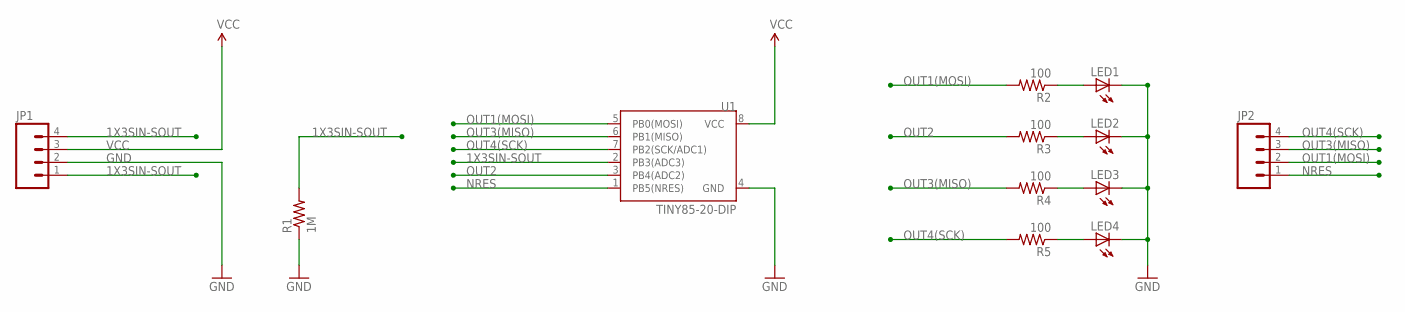
[picture p119: schematic LightBar.sch]

Parts:
JP1, JP2: M04PTH; 1X04
LED1, LED2, LED3, LED4: LEDSQR2X5; LED2X5
R1: 1M; R0603
R2, R3, R4, R5: 100; R0603
U1: TINY85-20-DIP; DIP08

Connections:
1X3SIN-SOUT: JP1.1, JP1.4, R1.2, U1.2 (PB3(ADC3))
GND: JP1.2, LED1.K (C), LED2.K (C), LED3.K (C), LED4.K (C), R1.1, U1.4 (GND)
unnamed: LED1.A, R2.1
unnamed: LED2.A, R3.1
unnamed: LED3.A, R4.1
unnamed: LED4.A, R5.1
NRES: JP2.1, U1.1 (PB5(NRES))
OUT1(MOSI): JP2.2, R2.2, U1.5 (PB0(MOSI))
OUT2: R3.2, U1.3 (PB4(ADC2))
OUT3(MISO): JP2.3, R4.2, U1.6 (PB1(MISO))
OUT4(SCK): JP2.4, R5.2, U1.7 (PB2(SCK/ADC1))
VCC: JP1.3, U1.8 (VCC)
