MakerWear/MakerWear/Modules/Action/Vibration/EagleDesigns/Vibration.sch

## EAGLE design Modules/Action/Vibration/EagleDesigns/Vibration.sch (2016-06-02)

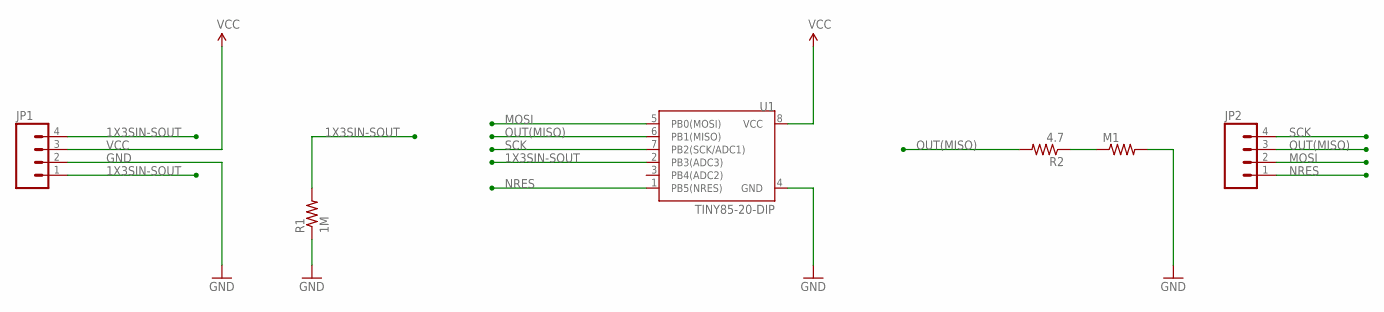
[picture p120: schematic Vibration.sch]

Parts:
JP1, JP2: M04PTH; 1X04
M1: 10OHM-1/4W-5%(PTH)VERT-KIT; AXIAL-0.1EZ
R1: 1M; R0603
R2: 4.7; R0603
U1: TINY85-20-DIP; DIP08

Connections:
1X3SIN-SOUT: JP1.1, JP1.4, R1.2, U1.2 (PB3(ADC3))
GND: JP1.2, M1.P$2 (2), R1.1, U1.4 (GND)
MOSI: JP2.2, U1.5 (PB0(MOSI))
unnamed: M1.P$1 (1), R2.1
NRES: JP2.1, U1.1 (PB5(NRES))
OUT(MISO): JP2.3, R2.2, U1.6 (PB1(MISO))
SCK: JP2.4, U1.7 (PB2(SCK/ADC1))
VCC: JP1.3, U1.8 (VCC)
