MakerWear/MakerWear/Modules/Other/WireRECV/EagleDesigns/WireRECV.sch

## EAGLE design Modules/Other/WireRECV/EagleDesigns/WireRECV.sch (2016-06-13)

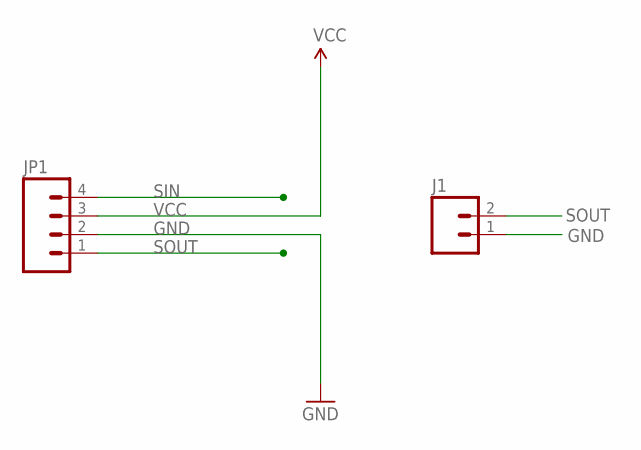
[picture p122: schematic WireRECV.sch]

Parts:
J1: M02PTH; 1X02
JP1: M04PTH; 1X04

Connections:
GND: J1.1, JP1.2
SIN: JP1.4
SOUT: J1.2, JP1.1
VCC: JP1.3
