MakerWear/MakerWear/Modules/Sensor/LightSensor/EagleDesigns/LightSensor.sch

## EAGLE design Modules/Sensor/LightSensor/EagleDesigns/LightSensor.sch (2016-06-02)

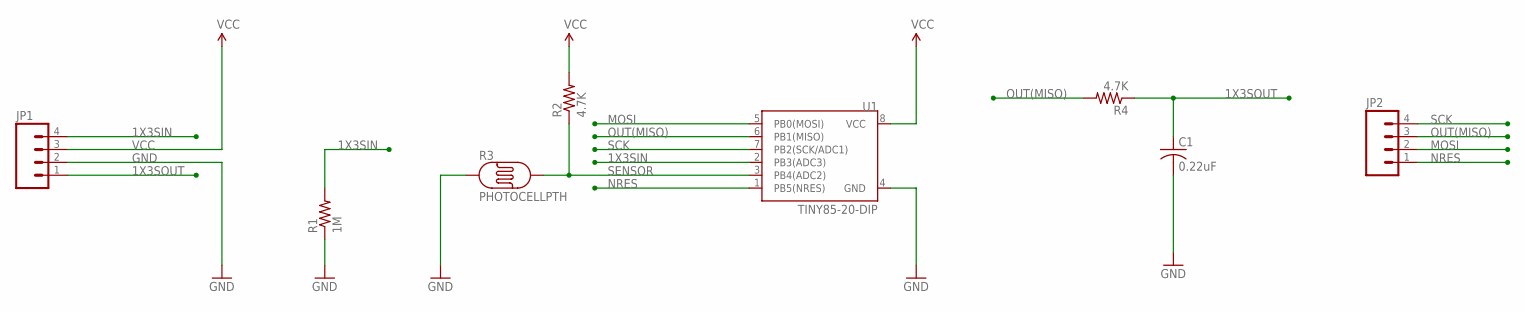
[picture p124: schematic LightSensor.sch]

Parts:
C1: 0.22uF; C0402
JP1, JP2: M04PTH; 1X04
R1: 1M; R0603
R2, R4: 4.7K; R0603
R3: PHOTOCELLPTH; PHOTOCELL
U1: TINY85-20-DIP; DIP08

Connections:
1X3SIN: JP1.4, R1.2, U1.2 (PB3(ADC3))
1X3SOUT: C1.1, JP1.1, R4.1
GND: C1.2, JP1.2, R1.1, R3.1, U1.4 (GND)
MOSI: JP2.2, U1.5 (PB0(MOSI))
NRES: JP2.1, U1.1 (PB5(NRES))
OUT(MISO): JP2.3, R4.2, U1.6 (PB1(MISO))
SCK: JP2.4, U1.7 (PB2(SCK/ADC1))
SENSOR: R2.1, R3.2, U1.3 (PB4(ADC2))
VCC: JP1.3, R2.2, U1.8 (VCC)
