MakerWear/MakerWear/Modules/Sensor/SunlightDetector/EagleDesigns/SunlightDetector.sch

## EAGLE design Modules/Sensor/SunlightDetector/EagleDesigns/SunlightDetector.sch (2016-06-02)

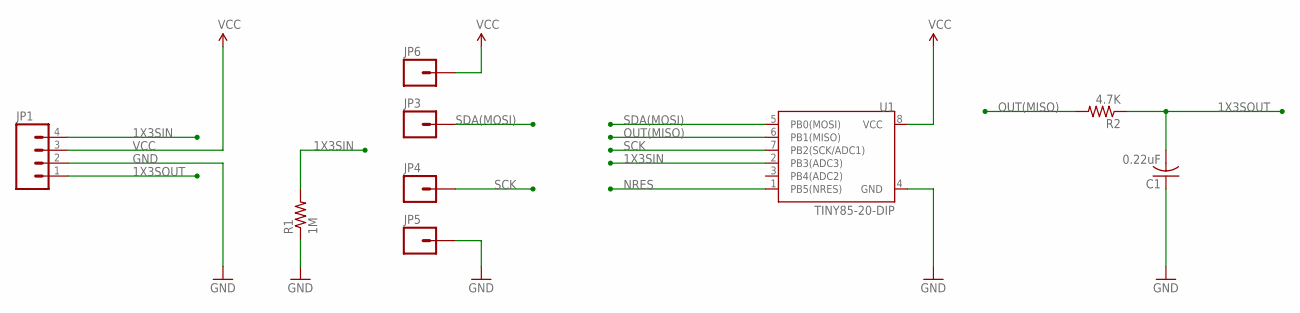
[picture p125: schematic SunlightDetector.sch]

Parts:
C1: 0.22uF; C0402
JP1: M04PTH; 1X04
JP3, JP4, JP5, JP6: M01PTH; 1X01
R1: 1M; R0603
R2: 4.7K; R0603
U1: TINY85-20-DIP; DIP08

Connections:
1X3SIN: JP1.4, R1.2, U1.2 (PB3(ADC3))
1X3SOUT: C1.2, JP1.1, R2.1
GND: C1.1, JP1.2, JP5.1, R1.1, U1.4 (GND)
NRES: U1.1 (PB5(NRES))
OUT(MISO): R2.2, U1.6 (PB1(MISO))
SCK: JP4.1, U1.7 (PB2(SCK/ADC1))
SDA(MOSI): JP3.1, U1.5 (PB0(MOSI))
VCC: JP1.3, JP6.1, U1.8 (VCC)
