MakerWear/MakerWear/Modules/Sensor/SunlightDetector/ArduinoCodes/SunlightDetectorArduino/SunlightDetectorArduino.ino

/*
**  SunlightDetectorATtiny.ino
**  MakerWear SunlightDetector Module's Arduino Program.
**
**  Changes voltage output proportional to amount of UV light
**
**
**  Arduino Pin Configurations:  
**
**  Arduino Pin SDA: Color Sensor SDA
**  Arduino Pin SCK: Color Sensor SCK
**  Arduino Pin 11: Module Output
**
**
**  Created on 10/19/15.
**  By Majeed Kazemitabaar
**
**  MakerWear Link:
**  Github Link:      github.com/myjeeed/MakerWear
**
*/

#include <Wire.h>
#include "Adafruit_SI1145.h"
//#include <FilteredAnalogInput.h>

//int input_pin = 3;                           //Pin 2 on ATtiny
int output_pin = 11;                          //Pin 6 on ATtiny
//int filter_size = 15;                        //Noise reduction filter size

//FilteredAnalogInput input(input_pin, filter_size);


Adafruit_SI1145 uv = Adafruit_SI1145();

void setup() {
  Serial.begin(9600);
  
  while (!uv.begin())
  {
    Serial.println("Didn't find SI1145 Sensor!");
    delay(500);
  }
  
  Serial.println("Connected!");
}

void loop() {
  float UVindex = uv.readUV()/100;
  
  int output_value = map((int)UVindex, 0, 12, 0, 255);
  analogWrite(output_pin, output_value);
  
  Serial.println(UVindex);
}
