MakerWear/MakerWear/Distance Sensor/DistanceSensorATtiny/DistanceSensorATtiny.ino

//TODO: Add resistor values in the code

//Pin Configurations
int input_pin = 3;           //Pin 2 on ATtiny
int ir_receiver_pin = 2;   //Pin 3 on ATtiny
int output_pin = 1;          //Pin 6 on ATtiny


void setup() {
  // put your setup code here, to run once:
  //Serial.begin(9600);
}

void loop() {
  int x = analogRead(ir_receiver_pin);
  float y = .000003*x*x*x - 0.0007*x*x + 0.1079*x + 8.2076;
  
  int input_value = analogRead(input_pin);
  
  int out_value = map(y, 8, 41, input_value/4, 0);

  if (out_value < 9)
    out_value = 0;
  
  analogWrite(output_pin, out_value);
  //Serial.println(out_value);
}
